dekuNukem/daytripper/resources/2.4 GHz Inverted F Antenna Eagle Library   fabiobaltieri_files/ifa-eagle.png

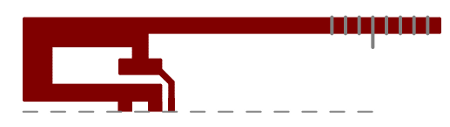
resources/2.4 GHz Inverted F Antenna Eagle Library fabiobaltieri_files/ifa-eagle.png
