dekuNukem/daytripper/resources/2.4 GHz Inverted F Antenna Eagle Library   fabiobaltieri_files/ifa.jpg

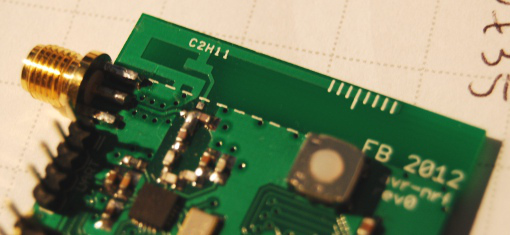
resources/2.4 GHz Inverted F Antenna Eagle Library fabiobaltieri_files/ifa.jpg
