dekuNukem/daytripper/resources/2.4 GHz Inverted F Antenna Eagle Library   fabiobaltieri_files/wpcom-gray-white.png

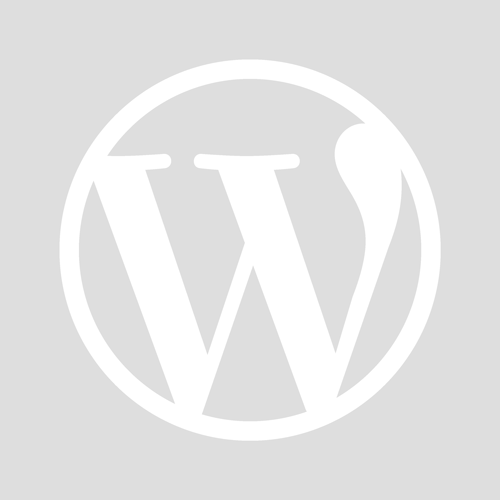
resources/2.4 GHz Inverted F Antenna Eagle Library fabiobaltieri_files/wpcom-gray-white.png
