dekuNukem/daytripper/firmware/distance_test/rx/MDK-ARM/rx/rx.htm

# Static Call Graph for image rx\rx.axf

#<CALLGRAPH># ARM Linker, 5060750: Last Updated: Sun Feb 24 13:35:41 2019

### Maximum Stack Usage = 220 bytes + Unknown(Cycles, Untraceable Function Pointers)

### Call chain for Maximum Stack Depth:

USB_IRQHandler ⇒ HAL_PCD_IRQHandler ⇒ HAL_PCD_ResumeCallback ⇒ SystemClock_Config ⇒ HAL_RCC_ClockConfig ⇒ HAL_RCC_GetSysClockFreq ⇒ __aeabi_uidivmod

### Mutually Recursive functions

- ADC1_IRQHandler ⇒ ADC1_IRQHandler
- HardFault_Handler ⇒ HardFault_Handler
- _Error_Handler ⇒ _Error_Handler

### Function Pointers

- ADC1_IRQHandler from startup_stm32f042x6.o(.text) referenced from startup_stm32f042x6.o(RESET)
- CEC_CAN_IRQHandler from startup_stm32f042x6.o(.text) referenced from startup_stm32f042x6.o(RESET)
- DMA1_Channel1_IRQHandler from startup_stm32f042x6.o(.text) referenced from startup_stm32f042x6.o(RESET)
- DMA1_Channel2_3_IRQHandler from startup_stm32f042x6.o(.text) referenced from startup_stm32f042x6.o(RESET)
- DMA1_Channel4_5_IRQHandler from startup_stm32f042x6.o(.text) referenced from startup_stm32f042x6.o(RESET)
- EXTI0_1_IRQHandler from startup_stm32f042x6.o(.text) referenced from startup_stm32f042x6.o(RESET)
- EXTI2_3_IRQHandler from startup_stm32f042x6.o(.text) referenced from startup_stm32f042x6.o(RESET)
- EXTI4_15_IRQHandler from startup_stm32f042x6.o(.text) referenced from startup_stm32f042x6.o(RESET)
- FLASH_IRQHandler from startup_stm32f042x6.o(.text) referenced from startup_stm32f042x6.o(RESET)
- HardFault_Handler from stm32f0xx_it.o(i.HardFault_Handler) referenced from startup_stm32f042x6.o(RESET)
- I2C1_IRQHandler from startup_stm32f042x6.o(.text) referenced from startup_stm32f042x6.o(RESET)
- NMI_Handler from stm32f0xx_it.o(i.NMI_Handler) referenced from startup_stm32f042x6.o(RESET)
- PVD_VDDIO2_IRQHandler from startup_stm32f042x6.o(.text) referenced from startup_stm32f042x6.o(RESET)
- PendSV_Handler from stm32f0xx_it.o(i.PendSV_Handler) referenced from startup_stm32f042x6.o(RESET)
- RCC_CRS_IRQHandler from startup_stm32f042x6.o(.text) referenced from startup_stm32f042x6.o(RESET)
- RTC_IRQHandler from startup_stm32f042x6.o(.text) referenced from startup_stm32f042x6.o(RESET)
- Reset_Handler from startup_stm32f042x6.o(.text) referenced from startup_stm32f042x6.o(RESET)
- SPI1_IRQHandler from startup_stm32f042x6.o(.text) referenced from startup_stm32f042x6.o(RESET)
- SPI2_IRQHandler from startup_stm32f042x6.o(.text) referenced from startup_stm32f042x6.o(RESET)
- SVC_Handler from stm32f0xx_it.o(i.SVC_Handler) referenced from startup_stm32f042x6.o(RESET)
- SysTick_Handler from stm32f0xx_it.o(i.SysTick_Handler) referenced from startup_stm32f042x6.o(RESET)
- SystemInit from system_stm32f0xx.o(i.SystemInit) referenced from startup_stm32f042x6.o(.text)
- TIM14_IRQHandler from startup_stm32f042x6.o(.text) referenced from startup_stm32f042x6.o(RESET)
- TIM16_IRQHandler from startup_stm32f042x6.o(.text) referenced from startup_stm32f042x6.o(RESET)
- TIM17_IRQHandler from startup_stm32f042x6.o(.text) referenced from startup_stm32f042x6.o(RESET)
- TIM1_BRK_UP_TRG_COM_IRQHandler from startup_stm32f042x6.o(.text) referenced from startup_stm32f042x6.o(RESET)
- TIM1_CC_IRQHandler from startup_stm32f042x6.o(.text) referenced from startup_stm32f042x6.o(RESET)
- TIM2_IRQHandler from startup_stm32f042x6.o(.text) referenced from startup_stm32f042x6.o(RESET)
- TIM3_IRQHandler from startup_stm32f042x6.o(.text) referenced from startup_stm32f042x6.o(RESET)
- TSC_IRQHandler from startup_stm32f042x6.o(.text) referenced from startup_stm32f042x6.o(RESET)
- USART1_IRQHandler from startup_stm32f042x6.o(.text) referenced from startup_stm32f042x6.o(RESET)
- USART2_IRQHandler from startup_stm32f042x6.o(.text) referenced from startup_stm32f042x6.o(RESET)
- USBD_FS_ConfigStrDescriptor from usbd_desc.o(i.USBD_FS_ConfigStrDescriptor) referenced from usbd_desc.o(.data)
- USBD_FS_DeviceDescriptor from usbd_desc.o(i.USBD_FS_DeviceDescriptor) referenced from usbd_desc.o(.data)
- USBD_FS_InterfaceStrDescriptor from usbd_desc.o(i.USBD_FS_InterfaceStrDescriptor) referenced from usbd_desc.o(.data)
- USBD_FS_LangIDStrDescriptor from usbd_desc.o(i.USBD_FS_LangIDStrDescriptor) referenced from usbd_desc.o(.data)
- USBD_FS_ManufacturerStrDescriptor from usbd_desc.o(i.USBD_FS_ManufacturerStrDescriptor) referenced from usbd_desc.o(.data)
- USBD_FS_ProductStrDescriptor from usbd_desc.o(i.USBD_FS_ProductStrDescriptor) referenced from usbd_desc.o(.data)
- USBD_FS_SerialStrDescriptor from usbd_desc.o(i.USBD_FS_SerialStrDescriptor) referenced from usbd_desc.o(.data)
- USBD_HID_DataIn from usbd_hid.o(i.USBD_HID_DataIn) referenced from usbd_hid.o(.data)
- USBD_HID_DeInit from usbd_hid.o(i.USBD_HID_DeInit) referenced from usbd_hid.o(.data)
- USBD_HID_GetCfgDesc from usbd_hid.o(i.USBD_HID_GetCfgDesc) referenced 3 times from usbd_hid.o(.data)
- USBD_HID_GetDeviceQualifierDesc from usbd_hid.o(i.USBD_HID_GetDeviceQualifierDesc) referenced from usbd_hid.o(.data)
- USBD_HID_Init from usbd_hid.o(i.USBD_HID_Init) referenced from usbd_hid.o(.data)
- USBD_HID_Setup from usbd_hid.o(i.USBD_HID_Setup) referenced from usbd_hid.o(.data)
- USB_IRQHandler from stm32f0xx_it.o(i.USB_IRQHandler) referenced from startup_stm32f042x6.o(RESET)
- WWDG_IRQHandler from startup_stm32f042x6.o(.text) referenced from startup_stm32f042x6.o(RESET)
- __main from entry.o(.ARM.Collect$$$$00000000) referenced from startup_stm32f042x6.o(.text)
- fputc from main.o(i.fputc) referenced from printf5.o(i.__0printf$5)
- main from main.o(i.main) referenced from entry9a.o(.ARM.Collect$$$$0000000B)

### Global Symbols

__main (Thumb, 0 bytes, Stack size unknown bytes, entry.o(.ARM.Collect$$$$00000000))
[Address Reference Count : 1]

- startup_stm32f042x6.o(.text)

_main_stk (Thumb, 0 bytes, Stack size unknown bytes, entry2.o(.ARM.Collect$$$$00000001))

_main_scatterload (Thumb, 0 bytes, Stack size unknown bytes, entry5.o(.ARM.Collect$$$$00000004))

[Calls]

- >> __scatterload

__main_after_scatterload (Thumb, 0 bytes, Stack size unknown bytes, entry5.o(.ARM.Collect$$$$00000004))

[Called By]

- >> __scatterload

_main_clock (Thumb, 0 bytes, Stack size unknown bytes, entry7b.o(.ARM.Collect$$$$00000008))

_main_cpp_init (Thumb, 0 bytes, Stack size unknown bytes, entry8b.o(.ARM.Collect$$$$0000000A))

_main_init (Thumb, 0 bytes, Stack size unknown bytes, entry9a.o(.ARM.Collect$$$$0000000B))

__rt_final_cpp (Thumb, 0 bytes, Stack size unknown bytes, entry10a.o(.ARM.Collect$$$$0000000D))

__rt_final_exit (Thumb, 0 bytes, Stack size unknown bytes, entry11a.o(.ARM.Collect$$$$0000000F))

Reset_Handler (Thumb, 38 bytes, Stack size 0 bytes, startup_stm32f042x6.o(.text))
[Address Reference Count : 1]

- startup_stm32f042x6.o(RESET)

ADC1_IRQHandler (Thumb, 0 bytes, Stack size 0 bytes, startup_stm32f042x6.o(.text))

[Calls]

- >> ADC1_IRQHandler

[Called By]

- >> ADC1_IRQHandler

[Address Reference Count : 1]

- startup_stm32f042x6.o(RESET)

CEC_CAN_IRQHandler (Thumb, 0 bytes, Stack size 0 bytes, startup_stm32f042x6.o(.text))
[Address Reference Count : 1]

- startup_stm32f042x6.o(RESET)

DMA1_Channel1_IRQHandler (Thumb, 0 bytes, Stack size 0 bytes, startup_stm32f042x6.o(.text))
[Address Reference Count : 1]

- startup_stm32f042x6.o(RESET)

DMA1_Channel2_3_IRQHandler (Thumb, 0 bytes, Stack size 0 bytes, startup_stm32f042x6.o(.text))
[Address Reference Count : 1]

- startup_stm32f042x6.o(RESET)

DMA1_Channel4_5_IRQHandler (Thumb, 0 bytes, Stack size 0 bytes, startup_stm32f042x6.o(.text))
[Address Reference Count : 1]

- startup_stm32f042x6.o(RESET)

EXTI0_1_IRQHandler (Thumb, 0 bytes, Stack size 0 bytes, startup_stm32f042x6.o(.text))
[Address Reference Count : 1]

- startup_stm32f042x6.o(RESET)

EXTI2_3_IRQHandler (Thumb, 0 bytes, Stack size 0 bytes, startup_stm32f042x6.o(.text))
[Address Reference Count : 1]

- startup_stm32f042x6.o(RESET)

EXTI4_15_IRQHandler (Thumb, 0 bytes, Stack size 0 bytes, startup_stm32f042x6.o(.text))
[Address Reference Count : 1]

- startup_stm32f042x6.o(RESET)

FLASH_IRQHandler (Thumb, 0 bytes, Stack size 0 bytes, startup_stm32f042x6.o(.text))
[Address Reference Count : 1]

- startup_stm32f042x6.o(RESET)

I2C1_IRQHandler (Thumb, 0 bytes, Stack size 0 bytes, startup_stm32f042x6.o(.text))
[Address Reference Count : 1]

- startup_stm32f042x6.o(RESET)

PVD_VDDIO2_IRQHandler (Thumb, 0 bytes, Stack size 0 bytes, startup_stm32f042x6.o(.text))
[Address Reference Count : 1]

- startup_stm32f042x6.o(RESET)

RCC_CRS_IRQHandler (Thumb, 0 bytes, Stack size 0 bytes, startup_stm32f042x6.o(.text))
[Address Reference Count : 1]

- startup_stm32f042x6.o(RESET)

RTC_IRQHandler (Thumb, 0 bytes, Stack size 0 bytes, startup_stm32f042x6.o(.text))
[Address Reference Count : 1]

- startup_stm32f042x6.o(RESET)

SPI1_IRQHandler (Thumb, 0 bytes, Stack size 0 bytes, startup_stm32f042x6.o(.text))
[Address Reference Count : 1]

- startup_stm32f042x6.o(RESET)

SPI2_IRQHandler (Thumb, 0 bytes, Stack size 0 bytes, startup_stm32f042x6.o(.text))
[Address Reference Count : 1]

- startup_stm32f042x6.o(RESET)

TIM14_IRQHandler (Thumb, 0 bytes, Stack size 0 bytes, startup_stm32f042x6.o(.text))
[Address Reference Count : 1]

- startup_stm32f042x6.o(RESET)

TIM16_IRQHandler (Thumb, 0 bytes, Stack size 0 bytes, startup_stm32f042x6.o(.text))
[Address Reference Count : 1]

- startup_stm32f042x6.o(RESET)

TIM17_IRQHandler (Thumb, 0 bytes, Stack size 0 bytes, startup_stm32f042x6.o(.text))
[Address Reference Count : 1]

- startup_stm32f042x6.o(RESET)

TIM1_BRK_UP_TRG_COM_IRQHandler (Thumb, 0 bytes, Stack size 0 bytes, startup_stm32f042x6.o(.text))
[Address Reference Count : 1]

- startup_stm32f042x6.o(RESET)

TIM1_CC_IRQHandler (Thumb, 0 bytes, Stack size 0 bytes, startup_stm32f042x6.o(.text))
[Address Reference Count : 1]

- startup_stm32f042x6.o(RESET)

TIM2_IRQHandler (Thumb, 0 bytes, Stack size 0 bytes, startup_stm32f042x6.o(.text))
[Address Reference Count : 1]

- startup_stm32f042x6.o(RESET)

TIM3_IRQHandler (Thumb, 0 bytes, Stack size 0 bytes, startup_stm32f042x6.o(.text))
[Address Reference Count : 1]

- startup_stm32f042x6.o(RESET)

TSC_IRQHandler (Thumb, 0 bytes, Stack size 0 bytes, startup_stm32f042x6.o(.text))
[Address Reference Count : 1]

- startup_stm32f042x6.o(RESET)

USART1_IRQHandler (Thumb, 0 bytes, Stack size 0 bytes, startup_stm32f042x6.o(.text))
[Address Reference Count : 1]

- startup_stm32f042x6.o(RESET)

USART2_IRQHandler (Thumb, 0 bytes, Stack size 0 bytes, startup_stm32f042x6.o(.text))
[Address Reference Count : 1]

- startup_stm32f042x6.o(RESET)

WWDG_IRQHandler (Thumb, 0 bytes, Stack size 0 bytes, startup_stm32f042x6.o(.text))
[Address Reference Count : 1]

- startup_stm32f042x6.o(RESET)

__aeabi_uidiv (Thumb, 0 bytes, Stack size 12 bytes, uidiv.o(.text), UNUSED)

__aeabi_uidivmod (Thumb, 44 bytes, Stack size 12 bytes, uidiv.o(.text))

[Stack]

- Max Depth = 12
- Call Chain = __aeabi_uidivmod

[Called By]

- >> USBD_LL_DataInStage
- >> SystemClock_Config
- >> HAL_InitTick
- >> HAL_RCC_GetSysClockFreq
- >> UART_SetConfig

__aeabi_llsr (Thumb, 34 bytes, Stack size 8 bytes, llushr.o(.text), UNUSED)

[Called By]

- >> __aeabi_uldivmod

_ll_ushift_r (Thumb, 0 bytes, Stack size 8 bytes, llushr.o(.text), UNUSED)

__aeabi_uldivmod (Thumb, 96 bytes, Stack size 48 bytes, uldiv.o(.text), UNUSED)

[Calls]

- >> __aeabi_llsr
- >> __aeabi_llsl

[Called By]

- >> _printf_core

__scatterload (Thumb, 28 bytes, Stack size 0 bytes, init.o(.text))

[Calls]

- >> __main_after_scatterload

[Called By]

- >> _main_scatterload

__scatterload_rt2 (Thumb, 0 bytes, Stack size 0 bytes, init.o(.text), UNUSED)

__aeabi_llsl (Thumb, 32 bytes, Stack size 8 bytes, llshl.o(.text), UNUSED)

[Called By]

- >> __aeabi_uldivmod

_ll_shift_l (Thumb, 0 bytes, Stack size 8 bytes, llshl.o(.text), UNUSED)

HAL_GPIO_Init (Thumb, 294 bytes, Stack size 24 bytes, stm32f0xx_hal_gpio.o(i.HAL_GPIO_Init))

[Stack]

- Max Depth = 24
- Call Chain = HAL_GPIO_Init

[Called By]

- >> MX_GPIO_Init
- >> HAL_UART_MspInit
- >> HAL_SPI_MspInit

HAL_GPIO_WritePin (Thumb, 12 bytes, Stack size 0 bytes, stm32f0xx_hal_gpio.o(i.HAL_GPIO_WritePin))

[Called By]

- >> main
- >> MX_GPIO_Init
- >> nrf24_csn_digitalWrite
- >> nrf24_ce_digitalWrite

HAL_GetTick (Thumb, 6 bytes, Stack size 0 bytes, stm32f0xx_hal.o(i.HAL_GetTick))

[Called By]

- >> HAL_UART_Transmit
- >> HAL_RCC_OscConfig
- >> HAL_RCC_ClockConfig
- >> HAL_RCCEx_PeriphCLKConfig
- >> HAL_SPI_TransmitReceive
- >> SPI_WaitFlagStateUntilTimeout
- >> SPI_WaitFifoStateUntilTimeout
- >> UART_WaitOnFlagUntilTimeout
- >> UART_CheckIdleState

HAL_HalfDuplex_Init (Thumb, 118 bytes, Stack size 16 bytes, stm32f0xx_hal_uart.o(i.HAL_HalfDuplex_Init))

[Stack]

- Max Depth = 100
- Call Chain = HAL_HalfDuplex_Init ⇒ UART_SetConfig ⇒ HAL_RCC_GetSysClockFreq ⇒ __aeabi_uidivmod

[Calls]

- >> HAL_UART_MspInit
- >> UART_SetConfig
- >> UART_CheckIdleState
- >> UART_AdvFeatureConfig

[Called By]

- >> MX_USART2_UART_Init

HAL_IncTick (Thumb, 10 bytes, Stack size 0 bytes, stm32f0xx_hal.o(i.HAL_IncTick))

[Called By]

- >> SysTick_Handler

HAL_Init (Thumb, 26 bytes, Stack size 8 bytes, stm32f0xx_hal.o(i.HAL_Init))

[Stack]

- Max Depth = 28
- Call Chain = HAL_Init ⇒ HAL_InitTick ⇒ __aeabi_uidivmod

[Calls]

- >> HAL_MspInit
- >> HAL_InitTick

[Called By]

- >> main

HAL_InitTick (Thumb, 34 bytes, Stack size 8 bytes, stm32f0xx_hal.o(i.HAL_InitTick))

[Stack]

- Max Depth = 20
- Call Chain = HAL_InitTick ⇒ __aeabi_uidivmod

[Calls]

- >> HAL_SYSTICK_Config
- >> HAL_RCC_GetHCLKFreq
- >> HAL_NVIC_SetPriority
- >> __aeabi_uidivmod

[Called By]

- >> HAL_RCC_ClockConfig
- >> HAL_Init

HAL_MspInit (Thumb, 74 bytes, Stack size 8 bytes, stm32f0xx_hal_msp.o(i.HAL_MspInit))

[Stack]

- Max Depth = 16
- Call Chain = HAL_MspInit ⇒ HAL_NVIC_SetPriority

[Calls]

- >> HAL_NVIC_SetPriority

[Called By]

- >> HAL_Init

HAL_NVIC_EnableIRQ (Thumb, 14 bytes, Stack size 0 bytes, stm32f0xx_hal_cortex.o(i.HAL_NVIC_EnableIRQ))

[Called By]

- >> HAL_PCD_MspInit

HAL_NVIC_SetPriority (Thumb, 8 bytes, Stack size 8 bytes, stm32f0xx_hal_cortex.o(i.HAL_NVIC_SetPriority))

[Stack]

- Max Depth = 8
- Call Chain = HAL_NVIC_SetPriority

[Calls]

- >> NVIC_SetPriority

[Called By]

- >> HAL_PCD_MspInit
- >> SystemClock_Config
- >> HAL_MspInit
- >> HAL_InitTick

HAL_PCDEx_PMAConfig (Thumb, 58 bytes, Stack size 8 bytes, stm32f0xx_hal_pcd_ex.o(i.HAL_PCDEx_PMAConfig))

[Stack]

- Max Depth = 8
- Call Chain = HAL_PCDEx_PMAConfig

[Called By]

- >> USBD_LL_Init

HAL_PCD_DataInStageCallback (Thumb, 24 bytes, Stack size 8 bytes, usbd_conf.o(i.HAL_PCD_DataInStageCallback))

[Stack]

- Max Depth = 84
- Call Chain = HAL_PCD_DataInStageCallback ⇒ USBD_LL_DataInStage ⇒ USBD_CtlContinueSendData ⇒ USBD_LL_Transmit ⇒ HAL_PCD_EP_Transmit ⇒ PCD_WritePMA

[Calls]

- >> USBD_LL_DataInStage

[Called By]

- >> PCD_EP_ISR_Handler

HAL_PCD_DataOutStageCallback (Thumb, 28 bytes, Stack size 8 bytes, usbd_conf.o(i.HAL_PCD_DataOutStageCallback))

[Stack]

- Max Depth = 68
- Call Chain = HAL_PCD_DataOutStageCallback ⇒ USBD_LL_DataOutStage ⇒ USBD_CtlSendStatus ⇒ USBD_LL_Transmit ⇒ HAL_PCD_EP_Transmit ⇒ PCD_WritePMA

[Calls]

- >> USBD_LL_DataOutStage

[Called By]

- >> PCD_EP_ISR_Handler

HAL_PCD_EP_Close (Thumb, 346 bytes, Stack size 20 bytes, stm32f0xx_hal_pcd.o(i.HAL_PCD_EP_Close))

[Stack]

- Max Depth = 20
- Call Chain = HAL_PCD_EP_Close

[Called By]

- >> USBD_LL_CloseEP

HAL_PCD_EP_ClrStall (Thumb, 166 bytes, Stack size 20 bytes, stm32f0xx_hal_pcd.o(i.HAL_PCD_EP_ClrStall))

[Stack]

- Max Depth = 20
- Call Chain = HAL_PCD_EP_ClrStall

[Called By]

- >> USBD_LL_ClearStallEP

HAL_PCD_EP_Open (Thumb, 652 bytes, Stack size 20 bytes, stm32f0xx_hal_pcd.o(i.HAL_PCD_EP_Open))

[Stack]

- Max Depth = 20
- Call Chain = HAL_PCD_EP_Open

[Called By]

- >> USBD_LL_OpenEP

HAL_PCD_EP_Receive (Thumb, 244 bytes, Stack size 20 bytes, stm32f0xx_hal_pcd.o(i.HAL_PCD_EP_Receive))

[Stack]

- Max Depth = 20
- Call Chain = HAL_PCD_EP_Receive

[Called By]

- >> USBD_LL_PrepareReceive
- >> PCD_EP_ISR_Handler

HAL_PCD_EP_SetStall (Thumb, 136 bytes, Stack size 20 bytes, stm32f0xx_hal_pcd.o(i.HAL_PCD_EP_SetStall))

[Stack]

- Max Depth = 20
- Call Chain = HAL_PCD_EP_SetStall

[Called By]

- >> USBD_LL_StallEP

HAL_PCD_EP_Transmit (Thumb, 222 bytes, Stack size 20 bytes, stm32f0xx_hal_pcd.o(i.HAL_PCD_EP_Transmit))

[Stack]

- Max Depth = 28
- Call Chain = HAL_PCD_EP_Transmit ⇒ PCD_WritePMA

[Calls]

- >> PCD_WritePMA

[Called By]

- >> USBD_LL_Transmit
- >> PCD_EP_ISR_Handler

HAL_PCD_IRQHandler (Thumb, 238 bytes, Stack size 16 bytes, stm32f0xx_hal_pcd.o(i.HAL_PCD_IRQHandler))

[Stack]

- Max Depth = 212
- Call Chain = HAL_PCD_IRQHandler ⇒ HAL_PCD_ResumeCallback ⇒ SystemClock_Config ⇒ HAL_RCC_ClockConfig ⇒ HAL_RCC_GetSysClockFreq ⇒ __aeabi_uidivmod

[Calls]

- >> HAL_PCD_SetAddress
- >> HAL_PCD_SuspendCallback
- >> HAL_PCD_SOFCallback
- >> HAL_PCD_ResumeCallback
- >> HAL_PCD_ResetCallback
- >> PCD_EP_ISR_Handler

[Called By]

- >> USB_IRQHandler

HAL_PCD_Init (Thumb, 154 bytes, Stack size 24 bytes, stm32f0xx_hal_pcd.o(i.HAL_PCD_Init))

[Stack]

- Max Depth = 40
- Call Chain = HAL_PCD_Init ⇒ HAL_PCD_MspInit ⇒ HAL_NVIC_SetPriority

[Calls]

- >> HAL_PCD_MspInit

[Called By]

- >> USBD_LL_Init

HAL_PCD_MspInit (Thumb, 46 bytes, Stack size 8 bytes, usbd_conf.o(i.HAL_PCD_MspInit))

[Stack]

- Max Depth = 16
- Call Chain = HAL_PCD_MspInit ⇒ HAL_NVIC_SetPriority

[Calls]

- >> HAL_NVIC_EnableIRQ
- >> HAL_NVIC_SetPriority

[Called By]

- >> HAL_PCD_Init

HAL_PCD_ResetCallback (Thumb, 24 bytes, Stack size 8 bytes, usbd_conf.o(i.HAL_PCD_ResetCallback))

[Stack]

- Max Depth = 60
- Call Chain = HAL_PCD_ResetCallback ⇒ USBD_LL_Reset ⇒ USBD_LL_OpenEP ⇒ HAL_PCD_EP_Open

[Calls]

- >> USBD_LL_SetSpeed
- >> USBD_LL_Reset

[Called By]

- >> HAL_PCD_IRQHandler

HAL_PCD_ResumeCallback (Thumb, 38 bytes, Stack size 8 bytes, usbd_conf.o(i.HAL_PCD_ResumeCallback))

[Stack]

- Max Depth = 196
- Call Chain = HAL_PCD_ResumeCallback ⇒ SystemClock_Config ⇒ HAL_RCC_ClockConfig ⇒ HAL_RCC_GetSysClockFreq ⇒ __aeabi_uidivmod

[Calls]

- >> USBD_LL_Resume
- >> SystemClock_Config

[Called By]

- >> HAL_PCD_IRQHandler

HAL_PCD_SOFCallback (Thumb, 16 bytes, Stack size 8 bytes, usbd_conf.o(i.HAL_PCD_SOFCallback))

[Stack]

- Max Depth = 16
- Call Chain = HAL_PCD_SOFCallback ⇒ USBD_LL_SOF

[Calls]

- >> USBD_LL_SOF

[Called By]

- >> HAL_PCD_IRQHandler

HAL_PCD_SetAddress (Thumb, 44 bytes, Stack size 0 bytes, stm32f0xx_hal_pcd.o(i.HAL_PCD_SetAddress))

[Called By]

- >> USBD_LL_SetUSBAddress
- >> HAL_PCD_IRQHandler

HAL_PCD_SetupStageCallback (Thumb, 22 bytes, Stack size 8 bytes, usbd_conf.o(i.HAL_PCD_SetupStageCallback))

[Stack]

- Max Depth = 116
- Call Chain = HAL_PCD_SetupStageCallback ⇒ USBD_LL_SetupStage ⇒ USBD_StdDevReq ⇒ USBD_GetDescriptor ⇒ USBD_CtlSendData ⇒ USBD_LL_Transmit ⇒ HAL_PCD_EP_Transmit ⇒ PCD_WritePMA

[Calls]

- >> USBD_LL_SetupStage

[Called By]

- >> PCD_EP_ISR_Handler

HAL_PCD_Start (Thumb, 18 bytes, Stack size 0 bytes, stm32f0xx_hal_pcd.o(i.HAL_PCD_Start))

[Called By]

- >> USBD_LL_Start

HAL_PCD_SuspendCallback (Thumb, 34 bytes, Stack size 8 bytes, usbd_conf.o(i.HAL_PCD_SuspendCallback))

[Stack]

- Max Depth = 8
- Call Chain = HAL_PCD_SuspendCallback

[Calls]

- >> USBD_LL_Suspend

[Called By]

- >> HAL_PCD_IRQHandler

HAL_RCCEx_PeriphCLKConfig (Thumb, 254 bytes, Stack size 24 bytes, stm32f0xx_hal_rcc_ex.o(i.HAL_RCCEx_PeriphCLKConfig))

[Stack]

- Max Depth = 24
- Call Chain = HAL_RCCEx_PeriphCLKConfig

[Calls]

- >> HAL_GetTick

[Called By]

- >> SystemClock_Config

HAL_RCC_ClockConfig (Thumb, 320 bytes, Stack size 24 bytes, stm32f0xx_hal_rcc.o(i.HAL_RCC_ClockConfig))

[Stack]

- Max Depth = 84
- Call Chain = HAL_RCC_ClockConfig ⇒ HAL_RCC_GetSysClockFreq ⇒ __aeabi_uidivmod

[Calls]

- >> HAL_GetTick
- >> HAL_InitTick
- >> HAL_RCC_GetSysClockFreq

[Called By]

- >> SystemClock_Config

HAL_RCC_GetHCLKFreq (Thumb, 6 bytes, Stack size 0 bytes, stm32f0xx_hal_rcc.o(i.HAL_RCC_GetHCLKFreq))

[Called By]

- >> SystemClock_Config
- >> HAL_InitTick

HAL_RCC_GetPCLK1Freq (Thumb, 20 bytes, Stack size 0 bytes, stm32f0xx_hal_rcc.o(i.HAL_RCC_GetPCLK1Freq))

[Called By]

- >> UART_SetConfig

HAL_RCC_GetSysClockFreq (Thumb, 90 bytes, Stack size 48 bytes, stm32f0xx_hal_rcc.o(i.HAL_RCC_GetSysClockFreq))

[Stack]

- Max Depth = 60
- Call Chain = HAL_RCC_GetSysClockFreq ⇒ __aeabi_uidivmod

[Calls]

- >> __aeabi_uidivmod

[Called By]

- >> HAL_RCC_ClockConfig
- >> UART_SetConfig

HAL_RCC_OscConfig (Thumb, 966 bytes, Stack size 32 bytes, stm32f0xx_hal_rcc.o(i.HAL_RCC_OscConfig))

[Stack]

- Max Depth = 32
- Call Chain = HAL_RCC_OscConfig

[Calls]

- >> HAL_GetTick

[Called By]

- >> SystemClock_Config

HAL_SPI_Init (Thumb, 184 bytes, Stack size 24 bytes, stm32f0xx_hal_spi.o(i.HAL_SPI_Init))

[Stack]

- Max Depth = 80
- Call Chain = HAL_SPI_Init ⇒ HAL_SPI_MspInit ⇒ HAL_GPIO_Init

[Calls]

- >> HAL_SPI_MspInit

[Called By]

- >> MX_SPI1_Init

HAL_SPI_MspInit (Thumb, 60 bytes, Stack size 32 bytes, stm32f0xx_hal_msp.o(i.HAL_SPI_MspInit))

[Stack]

- Max Depth = 56
- Call Chain = HAL_SPI_MspInit ⇒ HAL_GPIO_Init

[Calls]

- >> HAL_GPIO_Init

[Called By]

- >> HAL_SPI_Init

HAL_SPI_TransmitReceive (Thumb, 584 bytes, Stack size 48 bytes, stm32f0xx_hal_spi.o(i.HAL_SPI_TransmitReceive))

[Stack]

- Max Depth = 96
- Call Chain = HAL_SPI_TransmitReceive ⇒ SPI_EndRxTxTransaction ⇒ SPI_WaitFlagStateUntilTimeout

[Calls]

- >> HAL_GetTick
- >> SPI_EndRxTxTransaction

[Called By]

- >> spi_transfer

HAL_SYSTICK_CLKSourceConfig (Thumb, 20 bytes, Stack size 0 bytes, stm32f0xx_hal_cortex.o(i.HAL_SYSTICK_CLKSourceConfig))

[Called By]

- >> SystemClock_Config

HAL_SYSTICK_Callback (Thumb, 2 bytes, Stack size 0 bytes, stm32f0xx_hal_cortex.o(i.HAL_SYSTICK_Callback))

[Called By]

- >> HAL_SYSTICK_IRQHandler

HAL_SYSTICK_Config (Thumb, 38 bytes, Stack size 8 bytes, stm32f0xx_hal_cortex.o(i.HAL_SYSTICK_Config))

[Stack]

- Max Depth = 8
- Call Chain = HAL_SYSTICK_Config

[Calls]

- >> NVIC_SetPriority

[Called By]

- >> SystemClock_Config
- >> HAL_InitTick

HAL_SYSTICK_IRQHandler (Thumb, 8 bytes, Stack size 8 bytes, stm32f0xx_hal_cortex.o(i.HAL_SYSTICK_IRQHandler))

[Stack]

- Max Depth = 8
- Call Chain = HAL_SYSTICK_IRQHandler

[Calls]

- >> HAL_SYSTICK_Callback

[Called By]

- >> SysTick_Handler

HAL_UART_MspInit (Thumb, 62 bytes, Stack size 32 bytes, stm32f0xx_hal_msp.o(i.HAL_UART_MspInit))

[Stack]

- Max Depth = 56
- Call Chain = HAL_UART_MspInit ⇒ HAL_GPIO_Init

[Calls]

- >> HAL_GPIO_Init

[Called By]

- >> HAL_HalfDuplex_Init

HAL_UART_Transmit (Thumb, 200 bytes, Stack size 48 bytes, stm32f0xx_hal_uart.o(i.HAL_UART_Transmit))

[Stack]

- Max Depth = 88
- Call Chain = HAL_UART_Transmit ⇒ UART_WaitOnFlagUntilTimeout

[Calls]

- >> HAL_GetTick
- >> UART_WaitOnFlagUntilTimeout

[Called By]

- >> fputc

HardFault_Handler (Thumb, 2 bytes, Stack size 0 bytes, stm32f0xx_it.o(i.HardFault_Handler))

[Calls]

- >> HardFault_Handler

[Called By]

- >> HardFault_Handler

[Address Reference Count : 1]

- startup_stm32f042x6.o(RESET)

MX_USB_DEVICE_Init (Thumb, 28 bytes, Stack size 8 bytes, usb_device.o(i.MX_USB_DEVICE_Init))

[Stack]

- Max Depth = 64
- Call Chain = MX_USB_DEVICE_Init ⇒ USBD_Init ⇒ USBD_LL_Init ⇒ HAL_PCD_Init ⇒ HAL_PCD_MspInit ⇒ HAL_NVIC_SetPriority

[Calls]

- >> USBD_Start
- >> USBD_RegisterClass
- >> USBD_Init

[Called By]

- >> main

NMI_Handler (Thumb, 2 bytes, Stack size 0 bytes, stm32f0xx_it.o(i.NMI_Handler))
[Address Reference Count : 1]

- startup_stm32f042x6.o(RESET)

PCD_ReadPMA (Thumb, 42 bytes, Stack size 8 bytes, stm32f0xx_hal_pcd.o(i.PCD_ReadPMA))

[Stack]

- Max Depth = 8
- Call Chain = PCD_ReadPMA

[Called By]

- >> PCD_EP_ISR_Handler

PCD_WritePMA (Thumb, 38 bytes, Stack size 8 bytes, stm32f0xx_hal_pcd.o(i.PCD_WritePMA))

[Stack]

- Max Depth = 8
- Call Chain = PCD_WritePMA

[Called By]

- >> HAL_PCD_EP_Transmit
- >> PCD_EP_ISR_Handler

PendSV_Handler (Thumb, 2 bytes, Stack size 0 bytes, stm32f0xx_it.o(i.PendSV_Handler))
[Address Reference Count : 1]

- startup_stm32f042x6.o(RESET)

SVC_Handler (Thumb, 2 bytes, Stack size 0 bytes, stm32f0xx_it.o(i.SVC_Handler))
[Address Reference Count : 1]

- startup_stm32f042x6.o(RESET)

SysTick_Handler (Thumb, 12 bytes, Stack size 8 bytes, stm32f0xx_it.o(i.SysTick_Handler))

[Stack]

- Max Depth = 16
- Call Chain = SysTick_Handler ⇒ HAL_SYSTICK_IRQHandler

[Calls]

- >> HAL_SYSTICK_IRQHandler
- >> HAL_IncTick

[Address Reference Count : 1]

- startup_stm32f042x6.o(RESET)

SystemClock_Config (Thumb, 110 bytes, Stack size 104 bytes, main.o(i.SystemClock_Config))

[Stack]

- Max Depth = 188
- Call Chain = SystemClock_Config ⇒ HAL_RCC_ClockConfig ⇒ HAL_RCC_GetSysClockFreq ⇒ __aeabi_uidivmod

[Calls]

- >> HAL_SYSTICK_Config
- >> HAL_SYSTICK_CLKSourceConfig
- >> HAL_RCC_OscConfig
- >> HAL_RCC_GetHCLKFreq
- >> HAL_RCC_ClockConfig
- >> HAL_RCCEx_PeriphCLKConfig
- >> HAL_NVIC_SetPriority
- >> __aeabi_uidivmod

[Called By]

- >> HAL_PCD_ResumeCallback
- >> main

SystemInit (Thumb, 78 bytes, Stack size 0 bytes, system_stm32f0xx.o(i.SystemInit))
[Address Reference Count : 1]

- startup_stm32f042x6.o(.text)

UART_AdvFeatureConfig (Thumb, 202 bytes, Stack size 8 bytes, stm32f0xx_hal_uart.o(i.UART_AdvFeatureConfig))

[Stack]

- Max Depth = 8
- Call Chain = UART_AdvFeatureConfig

[Called By]

- >> HAL_HalfDuplex_Init

UART_CheckIdleState (Thumb, 96 bytes, Stack size 24 bytes, stm32f0xx_hal_uart.o(i.UART_CheckIdleState))

[Stack]

- Max Depth = 64
- Call Chain = UART_CheckIdleState ⇒ UART_WaitOnFlagUntilTimeout

[Calls]

- >> HAL_GetTick
- >> UART_WaitOnFlagUntilTimeout

[Called By]

- >> HAL_HalfDuplex_Init

UART_SetConfig (Thumb, 280 bytes, Stack size 24 bytes, stm32f0xx_hal_uart.o(i.UART_SetConfig))

[Stack]

- Max Depth = 84
- Call Chain = UART_SetConfig ⇒ HAL_RCC_GetSysClockFreq ⇒ __aeabi_uidivmod

[Calls]

- >> HAL_RCC_GetSysClockFreq
- >> HAL_RCC_GetPCLK1Freq
- >> __aeabi_uidivmod

[Called By]

- >> HAL_HalfDuplex_Init

UART_WaitOnFlagUntilTimeout (Thumb, 98 bytes, Stack size 40 bytes, stm32f0xx_hal_uart.o(i.UART_WaitOnFlagUntilTimeout))

[Stack]

- Max Depth = 40
- Call Chain = UART_WaitOnFlagUntilTimeout

[Calls]

- >> HAL_GetTick

[Called By]

- >> HAL_UART_Transmit
- >> UART_CheckIdleState

USBD_ClrClassConfig (Thumb, 16 bytes, Stack size 8 bytes, usbd_core.o(i.USBD_ClrClassConfig))

[Stack]

- Max Depth = 8
- Call Chain = USBD_ClrClassConfig

[Called By]

- >> USBD_SetConfig

USBD_CtlContinueRx (Thumb, 16 bytes, Stack size 8 bytes, usbd_ioreq.o(i.USBD_CtlContinueRx))

[Stack]

- Max Depth = 36
- Call Chain = USBD_CtlContinueRx ⇒ USBD_LL_PrepareReceive ⇒ HAL_PCD_EP_Receive

[Calls]

- >> USBD_LL_PrepareReceive

[Called By]

- >> USBD_LL_DataOutStage

USBD_CtlContinueSendData (Thumb, 16 bytes, Stack size 8 bytes, usbd_ioreq.o(i.USBD_CtlContinueSendData))

[Stack]

- Max Depth = 44
- Call Chain = USBD_CtlContinueSendData ⇒ USBD_LL_Transmit ⇒ HAL_PCD_EP_Transmit ⇒ PCD_WritePMA

[Calls]

- >> USBD_LL_Transmit

[Called By]

- >> USBD_LL_DataInStage

USBD_CtlError (Thumb, 20 bytes, Stack size 8 bytes, usbd_ctlreq.o(i.USBD_CtlError))

[Stack]

- Max Depth = 36
- Call Chain = USBD_CtlError ⇒ USBD_LL_StallEP ⇒ HAL_PCD_EP_SetStall

[Calls]

- >> USBD_LL_StallEP

[Called By]

- >> USBD_HID_Setup
- >> USBD_SetConfig
- >> USBD_GetDescriptor
- >> USBD_StdItfReq
- >> USBD_StdEPReq
- >> USBD_StdDevReq

USBD_CtlReceiveStatus (Thumb, 24 bytes, Stack size 8 bytes, usbd_ioreq.o(i.USBD_CtlReceiveStatus))

[Stack]

- Max Depth = 36
- Call Chain = USBD_CtlReceiveStatus ⇒ USBD_LL_PrepareReceive ⇒ HAL_PCD_EP_Receive

[Calls]

- >> USBD_LL_PrepareReceive

[Called By]

- >> USBD_LL_DataInStage

USBD_CtlSendData (Thumb, 28 bytes, Stack size 8 bytes, usbd_ioreq.o(i.USBD_CtlSendData))

[Stack]

- Max Depth = 44
- Call Chain = USBD_CtlSendData ⇒ USBD_LL_Transmit ⇒ HAL_PCD_EP_Transmit ⇒ PCD_WritePMA

[Calls]

- >> USBD_LL_Transmit

[Called By]

- >> USBD_HID_Setup
- >> USBD_GetDescriptor
- >> USBD_StdEPReq
- >> USBD_StdDevReq

USBD_CtlSendStatus (Thumb, 24 bytes, Stack size 8 bytes, usbd_ioreq.o(i.USBD_CtlSendStatus))

[Stack]

- Max Depth = 44
- Call Chain = USBD_CtlSendStatus ⇒ USBD_LL_Transmit ⇒ HAL_PCD_EP_Transmit ⇒ PCD_WritePMA

[Calls]

- >> USBD_LL_Transmit

[Called By]

- >> USBD_LL_DataOutStage
- >> USBD_SetConfig
- >> USBD_StdItfReq
- >> USBD_StdEPReq
- >> USBD_StdDevReq

USBD_FS_ConfigStrDescriptor (Thumb, 16 bytes, Stack size 8 bytes, usbd_desc.o(i.USBD_FS_ConfigStrDescriptor))

[Stack]

- Max Depth = 24
- Call Chain = USBD_FS_ConfigStrDescriptor ⇒ USBD_GetString

[Calls]

- >> USBD_GetString

[Address Reference Count : 1]

- usbd_desc.o(.data)

USBD_FS_DeviceDescriptor (Thumb, 8 bytes, Stack size 0 bytes, usbd_desc.o(i.USBD_FS_DeviceDescriptor))
[Address Reference Count : 1]

- usbd_desc.o(.data)

USBD_FS_InterfaceStrDescriptor (Thumb, 16 bytes, Stack size 8 bytes, usbd_desc.o(i.USBD_FS_InterfaceStrDescriptor))

[Stack]

- Max Depth = 24
- Call Chain = USBD_FS_InterfaceStrDescriptor ⇒ USBD_GetString

[Calls]

- >> USBD_GetString

[Address Reference Count : 1]

- usbd_desc.o(.data)

USBD_FS_LangIDStrDescriptor (Thumb, 8 bytes, Stack size 0 bytes, usbd_desc.o(i.USBD_FS_LangIDStrDescriptor))
[Address Reference Count : 1]

- usbd_desc.o(.data)

USBD_FS_ManufacturerStrDescriptor (Thumb, 16 bytes, Stack size 8 bytes, usbd_desc.o(i.USBD_FS_ManufacturerStrDescriptor))

[Stack]

- Max Depth = 24
- Call Chain = USBD_FS_ManufacturerStrDescriptor ⇒ USBD_GetString

[Calls]

- >> USBD_GetString

[Address Reference Count : 1]

- usbd_desc.o(.data)

USBD_FS_ProductStrDescriptor (Thumb, 16 bytes, Stack size 8 bytes, usbd_desc.o(i.USBD_FS_ProductStrDescriptor))

[Stack]

- Max Depth = 24
- Call Chain = USBD_FS_ProductStrDescriptor ⇒ USBD_GetString

[Calls]

- >> USBD_GetString

[Address Reference Count : 1]

- usbd_desc.o(.data)

USBD_FS_SerialStrDescriptor (Thumb, 16 bytes, Stack size 8 bytes, usbd_desc.o(i.USBD_FS_SerialStrDescriptor))

[Stack]

- Max Depth = 24
- Call Chain = USBD_FS_SerialStrDescriptor ⇒ USBD_GetString

[Calls]

- >> USBD_GetString

[Address Reference Count : 1]

- usbd_desc.o(.data)

USBD_GetString (Thumb, 68 bytes, Stack size 16 bytes, usbd_ctlreq.o(i.USBD_GetString))

[Stack]

- Max Depth = 16
- Call Chain = USBD_GetString

[Called By]

- >> USBD_FS_SerialStrDescriptor
- >> USBD_FS_ProductStrDescriptor
- >> USBD_FS_ManufacturerStrDescriptor
- >> USBD_FS_InterfaceStrDescriptor
- >> USBD_FS_ConfigStrDescriptor

USBD_Init (Thumb, 50 bytes, Stack size 8 bytes, usbd_core.o(i.USBD_Init))

[Stack]

- Max Depth = 56
- Call Chain = USBD_Init ⇒ USBD_LL_Init ⇒ HAL_PCD_Init ⇒ HAL_PCD_MspInit ⇒ HAL_NVIC_SetPriority

[Calls]

- >> USBD_LL_Init

[Called By]

- >> MX_USB_DEVICE_Init

USBD_LL_ClearStallEP (Thumb, 38 bytes, Stack size 8 bytes, usbd_conf.o(i.USBD_LL_ClearStallEP))

[Stack]

- Max Depth = 28
- Call Chain = USBD_LL_ClearStallEP ⇒ HAL_PCD_EP_ClrStall

[Calls]

- >> HAL_PCD_EP_ClrStall

[Called By]

- >> USBD_StdEPReq

USBD_LL_CloseEP (Thumb, 38 bytes, Stack size 8 bytes, usbd_conf.o(i.USBD_LL_CloseEP))

[Stack]

- Max Depth = 28
- Call Chain = USBD_LL_CloseEP ⇒ HAL_PCD_EP_Close

[Calls]

- >> HAL_PCD_EP_Close

[Called By]

- >> USBD_HID_DeInit

USBD_LL_DataInStage (Thumb, 182 bytes, Stack size 32 bytes, usbd_core.o(i.USBD_LL_DataInStage))

[Stack]

- Max Depth = 76
- Call Chain = USBD_LL_DataInStage ⇒ USBD_CtlContinueSendData ⇒ USBD_LL_Transmit ⇒ HAL_PCD_EP_Transmit ⇒ PCD_WritePMA

[Calls]

- >> USBD_LL_PrepareReceive
- >> __aeabi_uidivmod
- >> USBD_CtlReceiveStatus
- >> USBD_CtlContinueSendData

[Called By]

- >> HAL_PCD_DataInStageCallback

USBD_LL_DataOutStage (Thumb, 116 bytes, Stack size 16 bytes, usbd_core.o(i.USBD_LL_DataOutStage))

[Stack]

- Max Depth = 60
- Call Chain = USBD_LL_DataOutStage ⇒ USBD_CtlSendStatus ⇒ USBD_LL_Transmit ⇒ HAL_PCD_EP_Transmit ⇒ PCD_WritePMA

[Calls]

- >> USBD_CtlSendStatus
- >> USBD_CtlContinueRx

[Called By]

- >> HAL_PCD_DataOutStageCallback

USBD_LL_Init (Thumb, 102 bytes, Stack size 8 bytes, usbd_conf.o(i.USBD_LL_Init))

[Stack]

- Max Depth = 48
- Call Chain = USBD_LL_Init ⇒ HAL_PCD_Init ⇒ HAL_PCD_MspInit ⇒ HAL_NVIC_SetPriority

[Calls]

- >> HAL_PCD_Init
- >> HAL_PCDEx_PMAConfig
- >> _Error_Handler

[Called By]

- >> USBD_Init

USBD_LL_IsStallEP (Thumb, 36 bytes, Stack size 0 bytes, usbd_conf.o(i.USBD_LL_IsStallEP))

[Called By]

- >> USBD_StdEPReq

USBD_LL_OpenEP (Thumb, 44 bytes, Stack size 16 bytes, usbd_conf.o(i.USBD_LL_OpenEP))

[Stack]

- Max Depth = 36
- Call Chain = USBD_LL_OpenEP ⇒ HAL_PCD_EP_Open

[Calls]

- >> HAL_PCD_EP_Open

[Called By]

- >> USBD_LL_Reset
- >> USBD_HID_Init

USBD_LL_PrepareReceive (Thumb, 38 bytes, Stack size 8 bytes, usbd_conf.o(i.USBD_LL_PrepareReceive))

[Stack]

- Max Depth = 28
- Call Chain = USBD_LL_PrepareReceive ⇒ HAL_PCD_EP_Receive

[Calls]

- >> HAL_PCD_EP_Receive

[Called By]

- >> USBD_LL_DataInStage
- >> USBD_CtlReceiveStatus
- >> USBD_CtlContinueRx

USBD_LL_Reset (Thumb, 70 bytes, Stack size 16 bytes, usbd_core.o(i.USBD_LL_Reset))

[Stack]

- Max Depth = 52
- Call Chain = USBD_LL_Reset ⇒ USBD_LL_OpenEP ⇒ HAL_PCD_EP_Open

[Calls]

- >> USBD_LL_OpenEP

[Called By]

- >> HAL_PCD_ResetCallback

USBD_LL_Resume (Thumb, 12 bytes, Stack size 0 bytes, usbd_core.o(i.USBD_LL_Resume))

[Called By]

- >> HAL_PCD_ResumeCallback

USBD_LL_SOF (Thumb, 30 bytes, Stack size 8 bytes, usbd_core.o(i.USBD_LL_SOF))

[Stack]

- Max Depth = 8
- Call Chain = USBD_LL_SOF

[Called By]

- >> HAL_PCD_SOFCallback

USBD_LL_SetSpeed (Thumb, 6 bytes, Stack size 0 bytes, usbd_core.o(i.USBD_LL_SetSpeed))

[Called By]

- >> HAL_PCD_ResetCallback

USBD_LL_SetUSBAddress (Thumb, 38 bytes, Stack size 8 bytes, usbd_conf.o(i.USBD_LL_SetUSBAddress))

[Stack]

- Max Depth = 8
- Call Chain = USBD_LL_SetUSBAddress

[Calls]

- >> HAL_PCD_SetAddress

[Called By]

- >> USBD_StdDevReq

USBD_LL_SetupStage (Thumb, 94 bytes, Stack size 16 bytes, usbd_core.o(i.USBD_LL_SetupStage))

[Stack]

- Max Depth = 108
- Call Chain = USBD_LL_SetupStage ⇒ USBD_StdDevReq ⇒ USBD_GetDescriptor ⇒ USBD_CtlSendData ⇒ USBD_LL_Transmit ⇒ HAL_PCD_EP_Transmit ⇒ PCD_WritePMA

[Calls]

- >> USBD_LL_StallEP
- >> USBD_StdItfReq
- >> USBD_StdEPReq
- >> USBD_StdDevReq
- >> USBD_ParseSetupRequest

[Called By]

- >> HAL_PCD_SetupStageCallback

USBD_LL_StallEP (Thumb, 38 bytes, Stack size 8 bytes, usbd_conf.o(i.USBD_LL_StallEP))

[Stack]

- Max Depth = 28
- Call Chain = USBD_LL_StallEP ⇒ HAL_PCD_EP_SetStall

[Calls]

- >> HAL_PCD_EP_SetStall

[Called By]

- >> USBD_LL_SetupStage
- >> USBD_CtlError
- >> USBD_StdEPReq

USBD_LL_Start (Thumb, 38 bytes, Stack size 8 bytes, usbd_conf.o(i.USBD_LL_Start))

[Stack]

- Max Depth = 8
- Call Chain = USBD_LL_Start

[Calls]

- >> HAL_PCD_Start

[Called By]

- >> USBD_Start

USBD_LL_Suspend (Thumb, 16 bytes, Stack size 0 bytes, usbd_core.o(i.USBD_LL_Suspend))

[Called By]

- >> HAL_PCD_SuspendCallback

USBD_LL_Transmit (Thumb, 38 bytes, Stack size 8 bytes, usbd_conf.o(i.USBD_LL_Transmit))

[Stack]

- Max Depth = 36
- Call Chain = USBD_LL_Transmit ⇒ HAL_PCD_EP_Transmit ⇒ PCD_WritePMA

[Calls]

- >> HAL_PCD_EP_Transmit

[Called By]

- >> USBD_CtlSendData
- >> USBD_CtlSendStatus
- >> USBD_CtlContinueSendData

USBD_ParseSetupRequest (Thumb, 40 bytes, Stack size 0 bytes, usbd_ctlreq.o(i.USBD_ParseSetupRequest))

[Called By]

- >> USBD_LL_SetupStage

USBD_RegisterClass (Thumb, 22 bytes, Stack size 0 bytes, usbd_core.o(i.USBD_RegisterClass))

[Called By]

- >> MX_USB_DEVICE_Init

USBD_SetClassConfig (Thumb, 28 bytes, Stack size 8 bytes, usbd_core.o(i.USBD_SetClassConfig))

[Stack]

- Max Depth = 8
- Call Chain = USBD_SetClassConfig

[Called By]

- >> USBD_SetConfig

USBD_Start (Thumb, 10 bytes, Stack size 8 bytes, usbd_core.o(i.USBD_Start))

[Stack]

- Max Depth = 16
- Call Chain = USBD_Start ⇒ USBD_LL_Start

[Calls]

- >> USBD_LL_Start

[Called By]

- >> MX_USB_DEVICE_Init

USBD_StdDevReq (Thumb, 238 bytes, Stack size 24 bytes, usbd_ctlreq.o(i.USBD_StdDevReq))

[Stack]

- Max Depth = 92
- Call Chain = USBD_StdDevReq ⇒ USBD_GetDescriptor ⇒ USBD_CtlSendData ⇒ USBD_LL_Transmit ⇒ HAL_PCD_EP_Transmit ⇒ PCD_WritePMA

[Calls]

- >> USBD_LL_SetUSBAddress
- >> USBD_CtlSendData
- >> USBD_CtlError
- >> USBD_SetConfig
- >> USBD_GetDescriptor
- >> USBD_CtlSendStatus
- >> __ARM_common_switch8

[Called By]

- >> USBD_LL_SetupStage

USBD_StdEPReq (Thumb, 234 bytes, Stack size 24 bytes, usbd_ctlreq.o(i.USBD_StdEPReq))

[Stack]

- Max Depth = 68
- Call Chain = USBD_StdEPReq ⇒ USBD_CtlSendData ⇒ USBD_LL_Transmit ⇒ HAL_PCD_EP_Transmit ⇒ PCD_WritePMA

[Calls]

- >> USBD_LL_StallEP
- >> USBD_LL_IsStallEP
- >> USBD_LL_ClearStallEP
- >> USBD_CtlSendData
- >> USBD_CtlError
- >> USBD_CtlSendStatus

[Called By]

- >> USBD_LL_SetupStage

USBD_StdItfReq (Thumb, 58 bytes, Stack size 16 bytes, usbd_ctlreq.o(i.USBD_StdItfReq))

[Stack]

- Max Depth = 60
- Call Chain = USBD_StdItfReq ⇒ USBD_CtlSendStatus ⇒ USBD_LL_Transmit ⇒ HAL_PCD_EP_Transmit ⇒ PCD_WritePMA

[Calls]

- >> USBD_CtlError
- >> USBD_CtlSendStatus

[Called By]

- >> USBD_LL_SetupStage

USBD_static_free (Thumb, 2 bytes, Stack size 0 bytes, usbd_conf.o(i.USBD_static_free))

[Called By]

- >> USBD_HID_DeInit

USBD_static_malloc (Thumb, 4 bytes, Stack size 0 bytes, usbd_conf.o(i.USBD_static_malloc))

[Called By]

- >> USBD_HID_Init

USB_IRQHandler (Thumb, 10 bytes, Stack size 8 bytes, stm32f0xx_it.o(i.USB_IRQHandler))

[Stack]

- Max Depth = 220
- Call Chain = USB_IRQHandler ⇒ HAL_PCD_IRQHandler ⇒ HAL_PCD_ResumeCallback ⇒ SystemClock_Config ⇒ HAL_RCC_ClockConfig ⇒ HAL_RCC_GetSysClockFreq ⇒ __aeabi_uidivmod

[Calls]

- >> HAL_PCD_IRQHandler

[Address Reference Count : 1]

- startup_stm32f042x6.o(RESET)

_Error_Handler (Thumb, 2 bytes, Stack size 0 bytes, main.o(i._Error_Handler))

[Calls]

- >> _Error_Handler

[Called By]

- >> USBD_LL_Init
- >> _Error_Handler

__0printf$5 (Thumb, 24 bytes, Stack size 24 bytes, printf5.o(i.__0printf$5), UNUSED)

[Calls]

- >> _printf_core

__1printf$5 (Thumb, 0 bytes, Stack size 24 bytes, printf5.o(i.__0printf$5), UNUSED)

__2printf (Thumb, 0 bytes, Stack size 24 bytes, printf5.o(i.__0printf$5))

[Stack]

- Max Depth = 24
- Call Chain = __2printf

[Called By]

- >> main

__ARM_common_switch8 (Thumb, 26 bytes, Stack size 8 bytes, stm32f0xx_hal_dma.o(i.__ARM_common_switch8))

[Stack]

- Max Depth = 8
- Call Chain = __ARM_common_switch8

[Called By]

- >> USBD_GetDescriptor
- >> USBD_StdDevReq

__scatterload_copy (Thumb, 14 bytes, Stack size unknown bytes, handlers.o(i.__scatterload_copy), UNUSED)

__scatterload_null (Thumb, 2 bytes, Stack size unknown bytes, handlers.o(i.__scatterload_null), UNUSED)

__scatterload_zeroinit (Thumb, 14 bytes, Stack size unknown bytes, handlers.o(i.__scatterload_zeroinit), UNUSED)

fputc (Thumb, 18 bytes, Stack size 16 bytes, main.o(i.fputc))

[Stack]

- Max Depth = 104
- Call Chain = fputc ⇒ HAL_UART_Transmit ⇒ UART_WaitOnFlagUntilTimeout

[Calls]

- >> HAL_UART_Transmit

[Address Reference Count : 1]

- printf5.o(i.__0printf$5)

main (Thumb, 136 bytes, Stack size 0 bytes, main.o(i.main))

[Stack]

- Max Depth = 188
- Call Chain = main ⇒ SystemClock_Config ⇒ HAL_RCC_ClockConfig ⇒ HAL_RCC_GetSysClockFreq ⇒ __aeabi_uidivmod

[Calls]

- >> MX_USB_DEVICE_Init
- >> HAL_Init
- >> SystemClock_Config
- >> MX_USART2_UART_Init
- >> MX_SPI1_Init
- >> MX_GPIO_Init
- >> HAL_GPIO_WritePin
- >> nrf24_tx_address
- >> nrf24_rx_address
- >> nrf24_init
- >> nrf24_getData
- >> nrf24_dataReady
- >> nrf24_config
- >> __2printf

[Address Reference Count : 1]

- entry9a.o(.ARM.Collect$$$$0000000B)

nrf24_ce_digitalWrite (Thumb, 24 bytes, Stack size 8 bytes, radiopinfunctions.o(i.nrf24_ce_digitalWrite))

[Stack]

- Max Depth = 8
- Call Chain = nrf24_ce_digitalWrite

[Calls]

- >> HAL_GPIO_WritePin

[Called By]

- >> nrf24_rx_address
- >> nrf24_powerUpRx
- >> nrf24_init

nrf24_config (Thumb, 116 bytes, Stack size 8 bytes, nrf24.o(i.nrf24_config))

[Stack]

- Max Depth = 144
- Call Chain = nrf24_config ⇒ nrf24_powerUpRx ⇒ nrf24_configRegister ⇒ spi_transfer ⇒ HAL_SPI_TransmitReceive ⇒ SPI_EndRxTxTransaction ⇒ SPI_WaitFlagStateUntilTimeout

[Calls]

- >> nrf24_powerUpRx
- >> nrf24_configRegister

[Called By]

- >> main

nrf24_configRegister (Thumb, 36 bytes, Stack size 16 bytes, nrf24.o(i.nrf24_configRegister))

[Stack]

- Max Depth = 128
- Call Chain = nrf24_configRegister ⇒ spi_transfer ⇒ HAL_SPI_TransmitReceive ⇒ SPI_EndRxTxTransaction ⇒ SPI_WaitFlagStateUntilTimeout

[Calls]

- >> nrf24_csn_digitalWrite
- >> spi_transfer

[Called By]

- >> nrf24_powerUpRx
- >> nrf24_getData
- >> nrf24_config

nrf24_csn_digitalWrite (Thumb, 26 bytes, Stack size 8 bytes, radiopinfunctions.o(i.nrf24_csn_digitalWrite))

[Stack]

- Max Depth = 8
- Call Chain = nrf24_csn_digitalWrite

[Calls]

- >> HAL_GPIO_WritePin

[Called By]

- >> nrf24_writeRegister
- >> nrf24_readRegister
- >> nrf24_powerUpRx
- >> nrf24_init
- >> nrf24_getStatus
- >> nrf24_getData
- >> nrf24_configRegister

nrf24_dataReady (Thumb, 26 bytes, Stack size 8 bytes, nrf24.o(i.nrf24_dataReady))

[Stack]

- Max Depth = 168
- Call Chain = nrf24_dataReady ⇒ nrf24_rxFifoEmpty ⇒ nrf24_readRegister ⇒ nrf24_transferSync ⇒ spi_transfer ⇒ HAL_SPI_TransmitReceive ⇒ SPI_EndRxTxTransaction ⇒ SPI_WaitFlagStateUntilTimeout

[Calls]

- >> nrf24_rxFifoEmpty
- >> nrf24_getStatus

[Called By]

- >> main

nrf24_getData (Thumb, 44 bytes, Stack size 8 bytes, nrf24.o(i.nrf24_getData))

[Stack]

- Max Depth = 144
- Call Chain = nrf24_getData ⇒ nrf24_transferSync ⇒ spi_transfer ⇒ HAL_SPI_TransmitReceive ⇒ SPI_EndRxTxTransaction ⇒ SPI_WaitFlagStateUntilTimeout

[Calls]

- >> nrf24_csn_digitalWrite
- >> spi_transfer
- >> nrf24_transferSync
- >> nrf24_configRegister

[Called By]

- >> main

nrf24_getStatus (Thumb, 26 bytes, Stack size 8 bytes, nrf24.o(i.nrf24_getStatus))

[Stack]

- Max Depth = 120
- Call Chain = nrf24_getStatus ⇒ spi_transfer ⇒ HAL_SPI_TransmitReceive ⇒ SPI_EndRxTxTransaction ⇒ SPI_WaitFlagStateUntilTimeout

[Calls]

- >> nrf24_csn_digitalWrite
- >> spi_transfer

[Called By]

- >> nrf24_dataReady

nrf24_init (Thumb, 16 bytes, Stack size 8 bytes, nrf24.o(i.nrf24_init))

[Stack]

- Max Depth = 16
- Call Chain = nrf24_init ⇒ nrf24_csn_digitalWrite

[Calls]

- >> nrf24_csn_digitalWrite
- >> nrf24_ce_digitalWrite

[Called By]

- >> main

nrf24_powerUpRx (Thumb, 50 bytes, Stack size 8 bytes, nrf24.o(i.nrf24_powerUpRx))

[Stack]

- Max Depth = 136
- Call Chain = nrf24_powerUpRx ⇒ nrf24_configRegister ⇒ spi_transfer ⇒ HAL_SPI_TransmitReceive ⇒ SPI_EndRxTxTransaction ⇒ SPI_WaitFlagStateUntilTimeout

[Calls]

- >> nrf24_csn_digitalWrite
- >> nrf24_ce_digitalWrite
- >> spi_transfer
- >> nrf24_configRegister

[Called By]

- >> nrf24_config

nrf24_readRegister (Thumb, 40 bytes, Stack size 16 bytes, nrf24.o(i.nrf24_readRegister))

[Stack]

- Max Depth = 152
- Call Chain = nrf24_readRegister ⇒ nrf24_transferSync ⇒ spi_transfer ⇒ HAL_SPI_TransmitReceive ⇒ SPI_EndRxTxTransaction ⇒ SPI_WaitFlagStateUntilTimeout

[Calls]

- >> nrf24_csn_digitalWrite
- >> spi_transfer
- >> nrf24_transferSync

[Called By]

- >> nrf24_rxFifoEmpty

nrf24_rxFifoEmpty (Thumb, 22 bytes, Stack size 8 bytes, nrf24.o(i.nrf24_rxFifoEmpty))

[Stack]

- Max Depth = 160
- Call Chain = nrf24_rxFifoEmpty ⇒ nrf24_readRegister ⇒ nrf24_transferSync ⇒ spi_transfer ⇒ HAL_SPI_TransmitReceive ⇒ SPI_EndRxTxTransaction ⇒ SPI_WaitFlagStateUntilTimeout

[Calls]

- >> nrf24_readRegister

[Called By]

- >> nrf24_dataReady

nrf24_rx_address (Thumb, 28 bytes, Stack size 8 bytes, nrf24.o(i.nrf24_rx_address))

[Stack]

- Max Depth = 152
- Call Chain = nrf24_rx_address ⇒ nrf24_writeRegister ⇒ nrf24_transmitSync ⇒ spi_transfer ⇒ HAL_SPI_TransmitReceive ⇒ SPI_EndRxTxTransaction ⇒ SPI_WaitFlagStateUntilTimeout

[Calls]

- >> nrf24_ce_digitalWrite
- >> nrf24_writeRegister

[Called By]

- >> main

nrf24_transferSync (Thumb, 30 bytes, Stack size 24 bytes, nrf24.o(i.nrf24_transferSync))

[Stack]

- Max Depth = 136
- Call Chain = nrf24_transferSync ⇒ spi_transfer ⇒ HAL_SPI_TransmitReceive ⇒ SPI_EndRxTxTransaction ⇒ SPI_WaitFlagStateUntilTimeout

[Calls]

- >> spi_transfer

[Called By]

- >> nrf24_readRegister
- >> nrf24_getData

nrf24_transmitSync (Thumb, 26 bytes, Stack size 16 bytes, nrf24.o(i.nrf24_transmitSync))

[Stack]

- Max Depth = 128
- Call Chain = nrf24_transmitSync ⇒ spi_transfer ⇒ HAL_SPI_TransmitReceive ⇒ SPI_EndRxTxTransaction ⇒ SPI_WaitFlagStateUntilTimeout

[Calls]

- >> spi_transfer

[Called By]

- >> nrf24_writeRegister

nrf24_tx_address (Thumb, 26 bytes, Stack size 8 bytes, nrf24.o(i.nrf24_tx_address))

[Stack]

- Max Depth = 152
- Call Chain = nrf24_tx_address ⇒ nrf24_writeRegister ⇒ nrf24_transmitSync ⇒ spi_transfer ⇒ HAL_SPI_TransmitReceive ⇒ SPI_EndRxTxTransaction ⇒ SPI_WaitFlagStateUntilTimeout

[Calls]

- >> nrf24_writeRegister

[Called By]

- >> main

nrf24_writeRegister (Thumb, 40 bytes, Stack size 16 bytes, nrf24.o(i.nrf24_writeRegister))

[Stack]

- Max Depth = 144
- Call Chain = nrf24_writeRegister ⇒ nrf24_transmitSync ⇒ spi_transfer ⇒ HAL_SPI_TransmitReceive ⇒ SPI_EndRxTxTransaction ⇒ SPI_WaitFlagStateUntilTimeout

[Calls]

- >> nrf24_csn_digitalWrite
- >> spi_transfer
- >> nrf24_transmitSync

[Called By]

- >> nrf24_tx_address
- >> nrf24_rx_address

spi_transfer (Thumb, 32 bytes, Stack size 16 bytes, nrf24.o(i.spi_transfer))

[Stack]

- Max Depth = 112
- Call Chain = spi_transfer ⇒ HAL_SPI_TransmitReceive ⇒ SPI_EndRxTxTransaction ⇒ SPI_WaitFlagStateUntilTimeout

[Calls]

- >> HAL_SPI_TransmitReceive

[Called By]

- >> nrf24_writeRegister
- >> nrf24_transmitSync
- >> nrf24_transferSync
- >> nrf24_readRegister
- >> nrf24_powerUpRx
- >> nrf24_getStatus
- >> nrf24_getData
- >> nrf24_configRegister

### Local Symbols

MX_GPIO_Init (Thumb, 174 bytes, Stack size 48 bytes, main.o(i.MX_GPIO_Init))

[Stack]

- Max Depth = 72
- Call Chain = MX_GPIO_Init ⇒ HAL_GPIO_Init

[Calls]

- >> HAL_GPIO_Init
- >> HAL_GPIO_WritePin

[Called By]

- >> main

MX_SPI1_Init (Thumb, 66 bytes, Stack size 8 bytes, main.o(i.MX_SPI1_Init))

[Stack]

- Max Depth = 88
- Call Chain = MX_SPI1_Init ⇒ HAL_SPI_Init ⇒ HAL_SPI_MspInit ⇒ HAL_GPIO_Init

[Calls]

- >> HAL_SPI_Init

[Called By]

- >> main

MX_USART2_UART_Init (Thumb, 46 bytes, Stack size 8 bytes, main.o(i.MX_USART2_UART_Init))

[Stack]

- Max Depth = 108
- Call Chain = MX_USART2_UART_Init ⇒ HAL_HalfDuplex_Init ⇒ UART_SetConfig ⇒ HAL_RCC_GetSysClockFreq ⇒ __aeabi_uidivmod

[Calls]

- >> HAL_HalfDuplex_Init

[Called By]

- >> main

PCD_EP_ISR_Handler (Thumb, 802 bytes, Stack size 40 bytes, stm32f0xx_hal_pcd.o(i.PCD_EP_ISR_Handler))

[Stack]

- Max Depth = 156
- Call Chain = PCD_EP_ISR_Handler ⇒ HAL_PCD_SetupStageCallback ⇒ USBD_LL_SetupStage ⇒ USBD_StdDevReq ⇒ USBD_GetDescriptor ⇒ USBD_CtlSendData ⇒ USBD_LL_Transmit ⇒ HAL_PCD_EP_Transmit ⇒ PCD_WritePMA

[Calls]

- >> HAL_PCD_EP_Transmit
- >> HAL_PCD_EP_Receive
- >> HAL_PCD_SetupStageCallback
- >> HAL_PCD_DataOutStageCallback
- >> HAL_PCD_DataInStageCallback
- >> PCD_WritePMA
- >> PCD_ReadPMA

[Called By]

- >> HAL_PCD_IRQHandler

SPI_EndRxTxTransaction (Thumb, 76 bytes, Stack size 24 bytes, stm32f0xx_hal_spi.o(i.SPI_EndRxTxTransaction))

[Stack]

- Max Depth = 48
- Call Chain = SPI_EndRxTxTransaction ⇒ SPI_WaitFlagStateUntilTimeout

[Calls]

- >> SPI_WaitFlagStateUntilTimeout
- >> SPI_WaitFifoStateUntilTimeout

[Called By]

- >> HAL_SPI_TransmitReceive

SPI_WaitFifoStateUntilTimeout (Thumb, 150 bytes, Stack size 24 bytes, stm32f0xx_hal_spi.o(i.SPI_WaitFifoStateUntilTimeout))

[Stack]

- Max Depth = 24
- Call Chain = SPI_WaitFifoStateUntilTimeout

[Calls]

- >> HAL_GetTick

[Called By]

- >> SPI_EndRxTxTransaction

SPI_WaitFlagStateUntilTimeout (Thumb, 140 bytes, Stack size 24 bytes, stm32f0xx_hal_spi.o(i.SPI_WaitFlagStateUntilTimeout))

[Stack]

- Max Depth = 24
- Call Chain = SPI_WaitFlagStateUntilTimeout

[Calls]

- >> HAL_GetTick

[Called By]

- >> SPI_EndRxTxTransaction

NVIC_SetPriority (Thumb, 60 bytes, Stack size 0 bytes, stm32f0xx_hal_cortex.o(i.NVIC_SetPriority))

[Called By]

- >> HAL_SYSTICK_Config
- >> HAL_NVIC_SetPriority

USBD_GetDescriptor (Thumb, 224 bytes, Stack size 24 bytes, usbd_ctlreq.o(i.USBD_GetDescriptor))

[Stack]

- Max Depth = 68
- Call Chain = USBD_GetDescriptor ⇒ USBD_CtlSendData ⇒ USBD_LL_Transmit ⇒ HAL_PCD_EP_Transmit ⇒ PCD_WritePMA

[Calls]

- >> USBD_CtlSendData
- >> USBD_CtlError
- >> __ARM_common_switch8

[Called By]

- >> USBD_StdDevReq

USBD_SetConfig (Thumb, 108 bytes, Stack size 16 bytes, usbd_ctlreq.o(i.USBD_SetConfig))

[Stack]

- Max Depth = 60
- Call Chain = USBD_SetConfig ⇒ USBD_CtlSendStatus ⇒ USBD_LL_Transmit ⇒ HAL_PCD_EP_Transmit ⇒ PCD_WritePMA

[Calls]

- >> USBD_CtlError
- >> USBD_CtlSendStatus
- >> USBD_SetClassConfig
- >> USBD_ClrClassConfig

[Called By]

- >> USBD_StdDevReq

USBD_HID_DataIn (Thumb, 16 bytes, Stack size 0 bytes, usbd_hid.o(i.USBD_HID_DataIn))
[Address Reference Count : 1]

- usbd_hid.o(.data)

USBD_HID_DeInit (Thumb, 34 bytes, Stack size 8 bytes, usbd_hid.o(i.USBD_HID_DeInit))

[Stack]

- Max Depth = 36
- Call Chain = USBD_HID_DeInit ⇒ USBD_LL_CloseEP ⇒ HAL_PCD_EP_Close

[Calls]

- >> USBD_static_free
- >> USBD_LL_CloseEP

[Address Reference Count : 1]

- usbd_hid.o(.data)

USBD_HID_GetCfgDesc (Thumb, 8 bytes, Stack size 0 bytes, usbd_hid.o(i.USBD_HID_GetCfgDesc))
[Address Reference Count : 1]

- usbd_hid.o(.data)

USBD_HID_GetDeviceQualifierDesc (Thumb, 8 bytes, Stack size 0 bytes, usbd_hid.o(i.USBD_HID_GetDeviceQualifierDesc))
[Address Reference Count : 1]

- usbd_hid.o(.data)

USBD_HID_Init (Thumb, 46 bytes, Stack size 16 bytes, usbd_hid.o(i.USBD_HID_Init))

[Stack]

- Max Depth = 52
- Call Chain = USBD_HID_Init ⇒ USBD_LL_OpenEP ⇒ HAL_PCD_EP_Open

[Calls]

- >> USBD_static_malloc
- >> USBD_LL_OpenEP

[Address Reference Count : 1]

- usbd_hid.o(.data)

USBD_HID_Setup (Thumb, 154 bytes, Stack size 16 bytes, usbd_hid.o(i.USBD_HID_Setup))

[Stack]

- Max Depth = 60
- Call Chain = USBD_HID_Setup ⇒ USBD_CtlSendData ⇒ USBD_LL_Transmit ⇒ HAL_PCD_EP_Transmit ⇒ PCD_WritePMA

[Calls]

- >> USBD_CtlSendData
- >> USBD_CtlError

[Address Reference Count : 1]

- usbd_hid.o(.data)

_printf_core (Thumb, 688 bytes, Stack size 96 bytes, printf5.o(i._printf_core), UNUSED)

[Calls]

- >> __aeabi_uldivmod

[Called By]

- >> __0printf$5

### Undefined Global Symbols
