dekuNukem/daytripper/pcb/rev3/rx.brd

## EAGLE design pcb/rev3/rx.brd (2019-02-25, an earlier design)

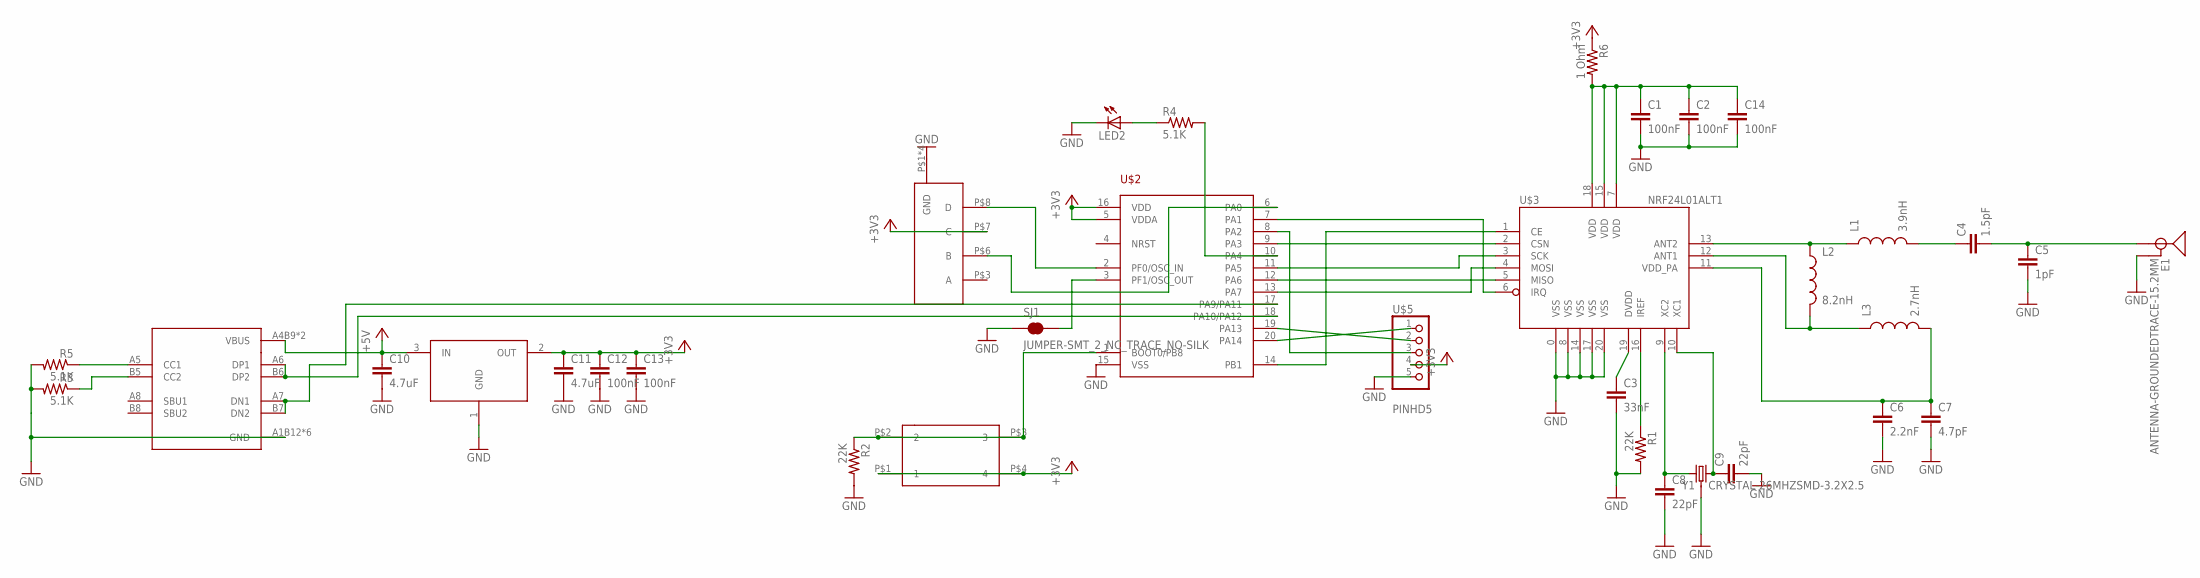
[picture p66: schematic rx.sch]

Parts:
C1, C2, C12, C13, C14: 100nF; 0805
C3: 33nF; 0805
C4: 1.5pF; 0805
C5: 1pF; 0805
C6: 2.2nF; 0805
C7: 4.7pF; 0805
C8, C9: 22pF; 0805
C10, C11: 4.7uF; 0805
E1: ANTENNA-GROUNDEDTRACE-15.2MM; TRACE_ANTENNA_2.4GHZ_15.2MM
L1: 3.9nH; 0805
L2: 8.2nH; 0805
L3: 2.7nH; 0805
LED2: LEDCHIP-LED0805; CHIP-LED0805
R1, R2: 22K; 0805
R3, R4, R5: 5.1K; 0805
R6: 1 Ohm; 0805
SJ1: JUMPER-SMT_2_NC_TRACE_NO-SILK; SMT-JUMPER_2_NC_TRACE_NO-SILK
U$1: SW_3POS_DEVSW_3POS_OFFICIAL; SW_3POS_FOOT_OFFICIAL
U$2: STM32F042F4; TSSOP20
U$3: NRF24L01ALT1; QFN20_ALT1
U$4: XC6206_DEV; SOT23R_INFINEON
U$5: PINHD5; 1X05
U$6: USBC_16P; USBC_16P_FOOT
U$10: 324_SW324_SWITCH_FOOT_HOLE; 342_SWICH_FOOT_HOLE
Y1: CRYSTAL-26MHZSMD-3.2X2.5; CRYSTAL-SMD-3.2X2.5MM

Connections:
+3V3: C11.1, C12.1, C13.1, R6.1, U$1.P$7 (C), U$2.5 (VDDA), U$2.16 (VDD), U$4.2 (OUT), U$5.4, U$10.P$1 (1), U$10.P$4 (4)
+5V: C10.1, U$4.3 (IN), U$6.A4B9 (VBUS), U$6.B4A9 (VBUS)
GND: C1.2, C2.2, C3.2, C5.2, C6.2, C7.2, C8.2, C9.2, C10.2, C11.2, C12.2, C13.2, C14.2, E1.GND, LED2.C, R1.2, R2.2, R3.2, R5.2, SJ1.1, U$1.P$1 (GND), U$1.P$2 (GND), U$1.P$4 (GND), U$1.P$5 (GND), U$2.15 (VSS), U$3.0 (VSS), U$3.8 (VSS), U$3.14 (VSS), U$3.17 (VSS), U$3.20 (VSS), U$4.1 (GND), U$5.5, U$6.A1B12 (GND), U$6.B11A12 (GND), U$6.P$13 (GND), U$6.P$14 (GND), U$6.P$15 (GND), U$6.P$16 (GND), Y1.2 (3), Y1.4 (3)
unnamed: C3.1, U$3.19 (DVDD)
unnamed: R1.1, U$3.16 (IREF)
unnamed: L1.1, L2.1, U$3.13 (ANT2)
unnamed: C4.1, L1.2
unnamed: C4.2, C5.1, E1.ANT (SIGNAL)
unnamed: L2.2, L3.1, U$3.12 (ANT1)
unnamed: C8.1, U$3.9 (XC2), Y1.1
unnamed: C6.1, C7.1, L3.2, U$3.11 (VDD_PA)
unnamed: C9.1, U$3.10 (XC1), Y1.3 (2)
unnamed: U$1.P$8 (D), U$2.2 (PF0/OSC_IN)
unnamed: R2.1, U$2.1 (BOOT0/PB8), U$10.P$2 (2), U$10.P$3 (3)
unnamed: U$2.17 (PA9/PA11), U$6.A7 (DN1), U$6.B7 (DN2)
unnamed: U$2.18 (PA10/PA12), U$6.A6 (DP1), U$6.B6 (DP2)
unnamed: U$2.12 (PA6), U$3.5 (MISO)
unnamed: U$2.13 (PA7), U$3.4 (MOSI)
unnamed: U$2.11 (PA5), U$3.3 (SCK)
unnamed: U$2.19 (PA13), U$5.2
unnamed: LED2.A, R4.1
unnamed: SJ1.2, U$2.3 (PF1/OSC_OUT)
unnamed: U$2.20 (PA14), U$5.1
unnamed: U$2.8 (PA2), U$5.3
unnamed: U$2.14 (PB1), U$3.1 (CE)
unnamed: R4.2, U$2.10 (PA4)
unnamed: U$2.9 (PA3), U$3.2 (CSN)
unnamed: R3.1, U$6.B5 (CC2)
unnamed: U$1.P$6 (B), U$2.6 (PA0)
unnamed: R5.1, U$6.A5 (CC1)
unnamed: C1.1, C2.1, C14.1, R6.2, U$3.7 (VDD), U$3.15 (VDD), U$3.18 (VDD)
unnamed: U$2.7 (PA1), U$3.6 (IRQ)

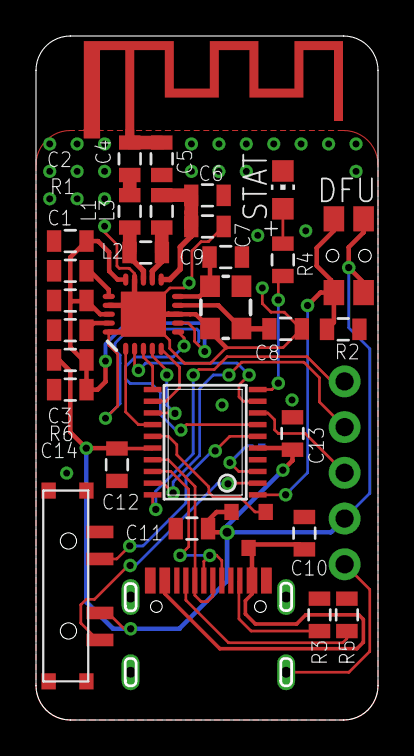
[picture p67: board pcb/rev3/rx.brd from above]

Board: 2 copper layers, 19.0 x 38.0 mm, 34 parts (1 on the bottom side), 32 nets.
