dekuNukem/daytripper/pcb/misc/rxSD.brd

## EAGLE design pcb/misc/rxSD.brd (2018-10-05)

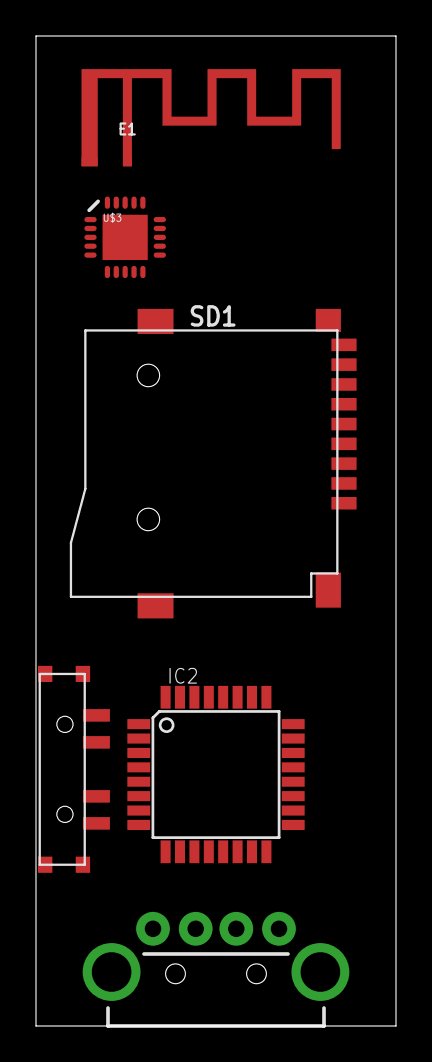
[picture p68: board rxSD.brd from above]

Board: 2 copper layers, 20.0 x 55.0 mm, 6 parts (0 on the bottom side), 2 nets, no tracks yet.

Parts:
E1: ANTENNA-GROUNDEDTRACE-15.2MM; TRACE_ANTENNA_2.4GHZ_15.2MM
IC2: STM32F042K6; TQFP32-08
J1: USB_A_PTH_MALE; USB-A-H
SD1: TF-HOLDER; TF-PULL
U$1: SW_3POS_DEVSW_3POS_OFFICIAL; SW_3POS_FOOT_OFFICIAL
U$3: NRF24L01ALT1; QFN20_ALT1

Connections:
VDD: SD1.4, U$3.7, U$3.15, U$3.18
VSS: SD1.6, U$3.0, U$3.8, U$3.14, U$3.17, U$3.20
