dekuNukem/daytripper/pcb/misc/rx.brd

## EAGLE design pcb/misc/rx.brd (2018-10-15)

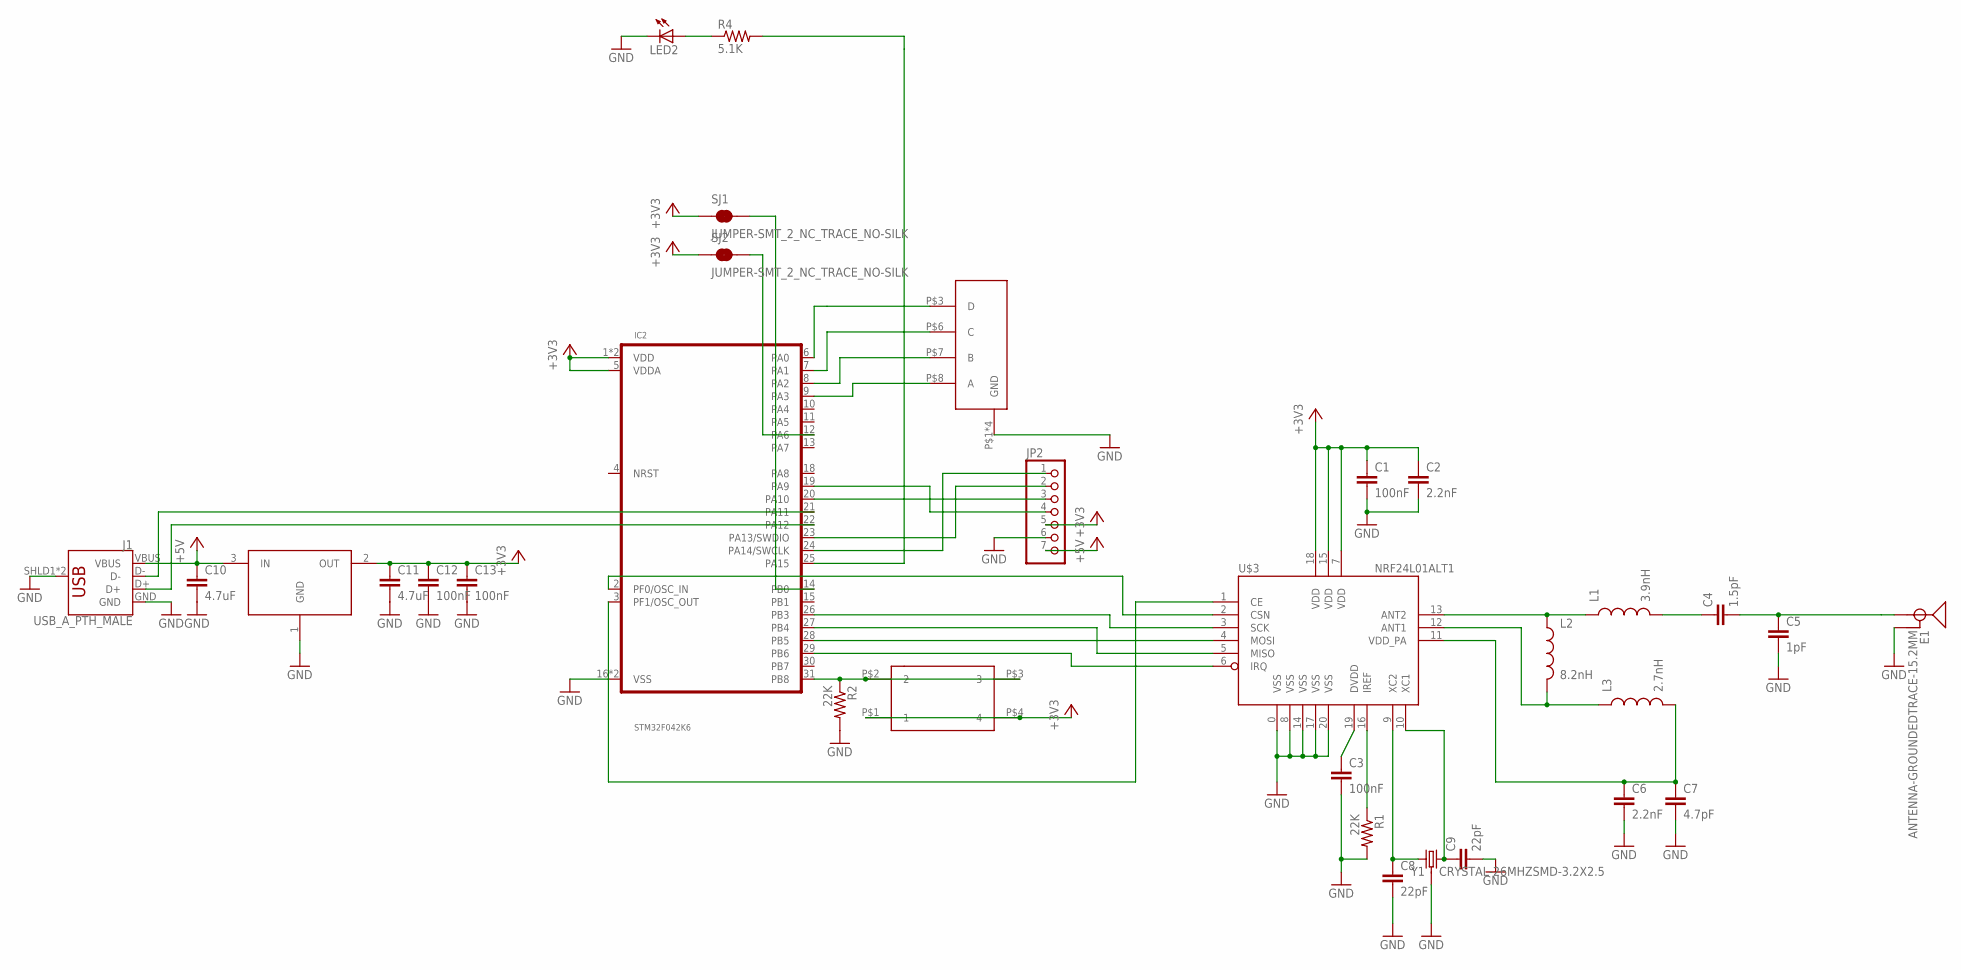
[picture p69: schematic rx.sch]

Parts:
C1, C3, C12, C13: 100nF; 0805
C2, C6: 2.2nF; 0805
C4: 1.5pF; 0805
C5: 1pF; 0805
C7: 4.7pF; 0805
C8, C9: 22pF; 0805
C10, C11: 4.7uF; 0805
E1: ANTENNA-GROUNDEDTRACE-15.2MM; TRACE_ANTENNA_2.4GHZ_15.2MM
IC2: STM32F042K6; TQFP32-08
J1: USB_A_PTH_MALE; USB-A-H
JP2: PINHD-1X8CLEANBIG; 1X08-CLEANBIG
L1: 3.9nH; 0805
L2: 8.2nH; 0805
L3: 2.7nH; 0805
LED2: LEDCHIP-LED0805; CHIP-LED0805
R1, R2: 22K; 0805
R4: 5.1K; 0805
SJ1, SJ2: JUMPER-SMT_2_NC_TRACE_NO-SILK; SMT-JUMPER_2_NC_TRACE_NO-SILK
U$1: SW_3POS_DEVSW_3POS_OFFICIAL; SW_3POS_FOOT_OFFICIAL
U$3: NRF24L01ALT1; QFN20_ALT1
U$4: XC6206_DEV; SOT23R_INFINEON
U$10: 324_SW; 342_SWICH_FOOT
Y1: CRYSTAL-26MHZSMD-3.2X2.5; CRYSTAL-SMD-3.2X2.5MM

Connections:
+3V3: C1.1, C2.1, C11.1, C12.1, C13.1, IC2.1 (VDD), IC2.5 (VDDA), IC2.17 (VDD), JP2.5, SJ1.1, SJ2.1, U$3.7 (VDD), U$3.15 (VDD), U$3.18 (VDD), U$4.2 (OUT), U$10.P$1 (1), U$10.P$4 (4)
+5V: C10.1, J1.VBUS, JP2.7, U$4.3 (IN)
GND: C1.2, C2.2, C3.2, C5.2, C6.2, C7.2, C8.2, C9.2, C10.2, C11.2, C12.2, C13.2, E1.GND, IC2.16 (VSS), IC2.32 (VSS), J1.GND, J1.SHLD1 (SHIELD), J1.SHLD2 (SHIELD), JP2.6, LED2.C, R1.2, R2.2, U$1.P$1 (GND), U$1.P$2 (GND), U$1.P$4 (GND), U$1.P$5 (GND), U$3.0 (VSS), U$3.8 (VSS), U$3.14 (VSS), U$3.17 (VSS), U$3.20 (VSS), U$4.1 (GND), Y1.2 (3), Y1.4 (3)
unnamed: C3.1, U$3.19 (DVDD)
unnamed: R1.1, U$3.16 (IREF)
unnamed: L1.1, L2.1, U$3.13 (ANT2)
unnamed: C4.1, L1.2
unnamed: C4.2, C5.1, E1.ANT (SIGNAL)
unnamed: L2.2, L3.1, U$3.12 (ANT1)
unnamed: C8.1, U$3.9 (XC2), Y1.1
unnamed: C6.1, C7.1, L3.2, U$3.11 (VDD_PA)
unnamed: C9.1, U$3.10 (XC1), Y1.3 (2)
unnamed: IC2.6 (PA0), U$1.P$3 (D)
unnamed: IC2.31 (PB8), R2.1, U$10.P$2 (2), U$10.P$3 (3)
unnamed: IC2.21 (PA11), J1.D-
unnamed: IC2.22 (PA12), J1.D+
unnamed: IC2.28 (PB5), U$3.4 (MOSI)
unnamed: IC2.27 (PB4), U$3.5 (MISO)
unnamed: IC2.26 (PB3), U$3.3 (SCK)
unnamed: IC2.29 (PB6), U$3.6 (IRQ)
unnamed: LED2.A, R4.1
unnamed: IC2.2 (PF0/OSC_IN), U$3.2 (CSN)
unnamed: IC2.3 (PF1/OSC_OUT), U$3.1 (CE)
unnamed: IC2.24 (PA14/SWCLK), JP2.1
unnamed: IC2.23 (PA13/SWDIO), JP2.2
unnamed: IC2.20 (PA10), JP2.3
unnamed: IC2.19 (PA9), JP2.4
unnamed: IC2.7 (PA1), U$1.P$6 (C)
unnamed: IC2.8 (PA2), U$1.P$7 (B)
unnamed: IC2.9 (PA3), U$1.P$8 (A)
unnamed: IC2.25 (PA15), R4.2
unnamed: IC2.12 (PA6), SJ2.2
unnamed: IC2.14 (PB0), SJ1.2
