dekuNukem/daytripper/pcb/misc/rx.brd

## EAGLE design pcb/misc/rx.brd (continued)

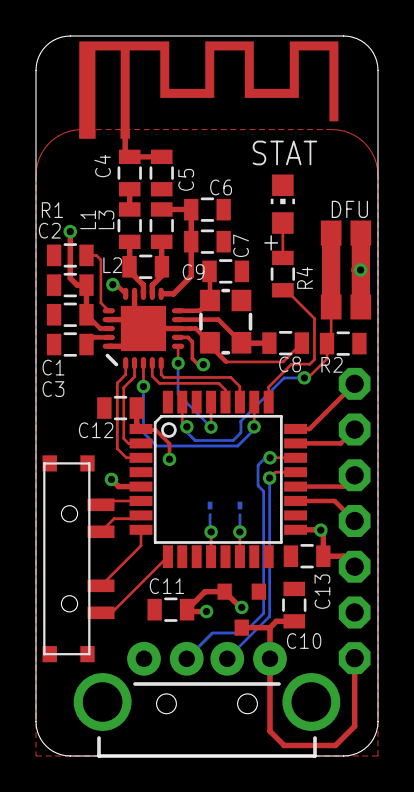
[picture p70: board pcb/misc/rx.brd from above]

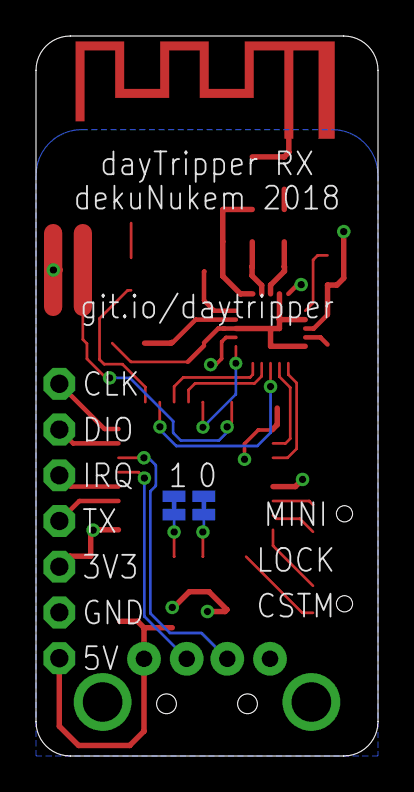
[picture p71: board pcb/misc/rx.brd from below]

Board: 2 copper layers, 19.0 x 40.0 mm, 31 parts (2 on the bottom side), 33 nets.
