dekuNukem/daytripper/pcb/misc/nRF24L01-Chip-v13/nRF24L01-Chip-v13.brd

## EAGLE design pcb/misc/nRF24L01-Chip-v13/nRF24L01-Chip-v13.brd (2018-08-13)

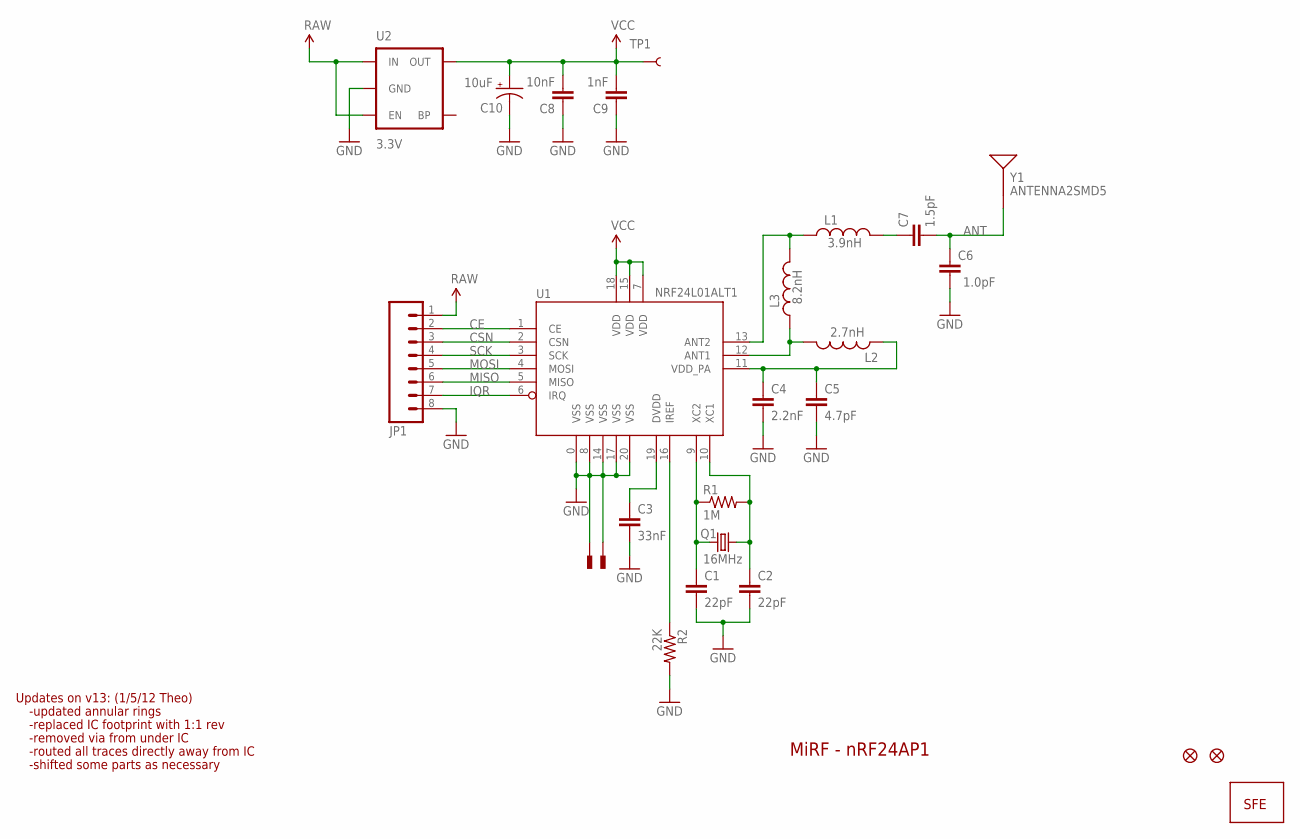
[picture p72: schematic nRF24L01-Chip-v13.sch]

Parts:
C1, C2: 22pF; 0402-CAP
C3: 33nF; 0402-CAP
C4: 2.2nF; 0402-CAP
C5: 4.7pF; 0402-CAP
C6: 1.0pF; 0402-CAP
C7: 1.5pF; 0402-CAP
C8: 10nF; 0402-CAP
C9: 1nF; 0402-CAP
C10: 10uF; EIA3216
JP1: M081X08; 1X08
JP2, JP3: FIDUCIALUFIDUCIAL; MICRO-FIDUCIAL
L1: 3.9nH; C0402
L2: 2.7nH; C0402
L3: 8.2nH; C0402
Q1: 16MHz; CRYSTAL-SMD-5X3
R1: 1M; 0402-RES
R2: 22K; 0402-RES
TP1: TEST-POINT3X5; PAD.03X.05
U1: NRF24L01ALT1; QFN20_ALT1
U2: 3.3V; SOT23-5
U$1, U$4: PAD; PAD-0.008
U$5: LOGO-SFENEW; SFE-NEW-WEBLOGO
Y1: ANTENNA2SMD5; ANTENNA-CHIP5

Connections:
ANT: C6.2, C7.2, Y1.FEED
CE: JP1.2, U1.1 (CE)
CSN: JP1.3, U1.2 (CSN)
GND: C1.2, C2.2, C3.2, C4.2, C5.2, C6.1, C8.1, C9.1, C10.C (-), JP1.8, R2.2, U1.0 (VSS), U1.8 (VSS), U1.14 (VSS), U1.17 (VSS), U1.20 (VSS), U2.2 (GND), U$1.P$1, U$4.P$1
IQR: JP1.7, U1.6 (IRQ)
MISO: JP1.6, U1.5 (MISO)
MOSI: JP1.5, U1.4 (MOSI)
unnamed: C1.1, Q1.1, R1.1, U1.9 (XC2)
unnamed: C2.1, Q1.3 (2), R1.2, U1.10 (XC1)
unnamed: L2.2, L3.1, U1.12 (ANT1)
unnamed: R2.1, U1.16 (IREF)
unnamed: C3.1, U1.19 (DVDD)
unnamed: L1.1, L3.2, U1.13 (ANT2)
unnamed: C4.1, C5.1, L2.1, U1.11 (VDD_PA)
unnamed: C7.1, L1.2
RAW: JP1.1, U2.1 (IN), U2.3 (EN)
SCK: JP1.4, U1.3 (SCK)
VCC: C8.2, C9.2, C10.A (+), TP1.P$1, U1.7 (VDD), U1.15 (VDD), U1.18 (VDD), U2.5 (OUT)

Notes on the sheet:
MiRF - nRF24AP1
Updates on v13: (1/5/12 Theo)
-updated annular rings
-replaced IC footprint with 1:1 rev
-removed via from under IC
-routed all traces directly away from IC
-shifted some parts as necessary

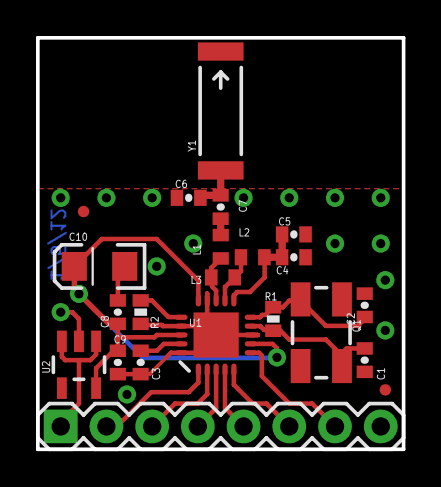
[picture p73: board nRF24L01-Chip-v13.brd from above]

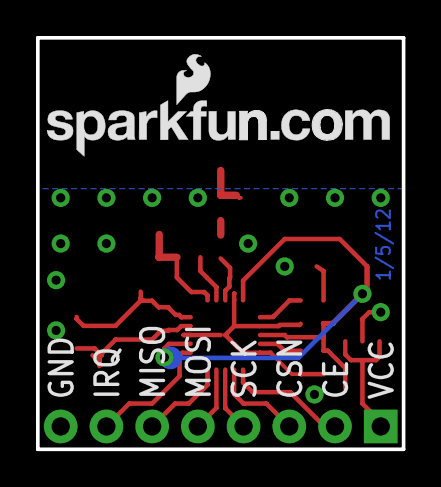
[picture p74: board nRF24L01-Chip-v13.brd from below]

Board: 2 copper layers, 20.3 x 22.9 mm, 26 parts (2 on the bottom side), 18 nets.
