dekuNukem/daytripper/pcb/misc/CC2541_Breakout_Board_Eagle_files/CC2541_Breakout_Board.brd

## EAGLE design pcb/misc/CC2541_Breakout_Board_Eagle_files/CC2541_Breakout_Board.brd (2018-10-05)

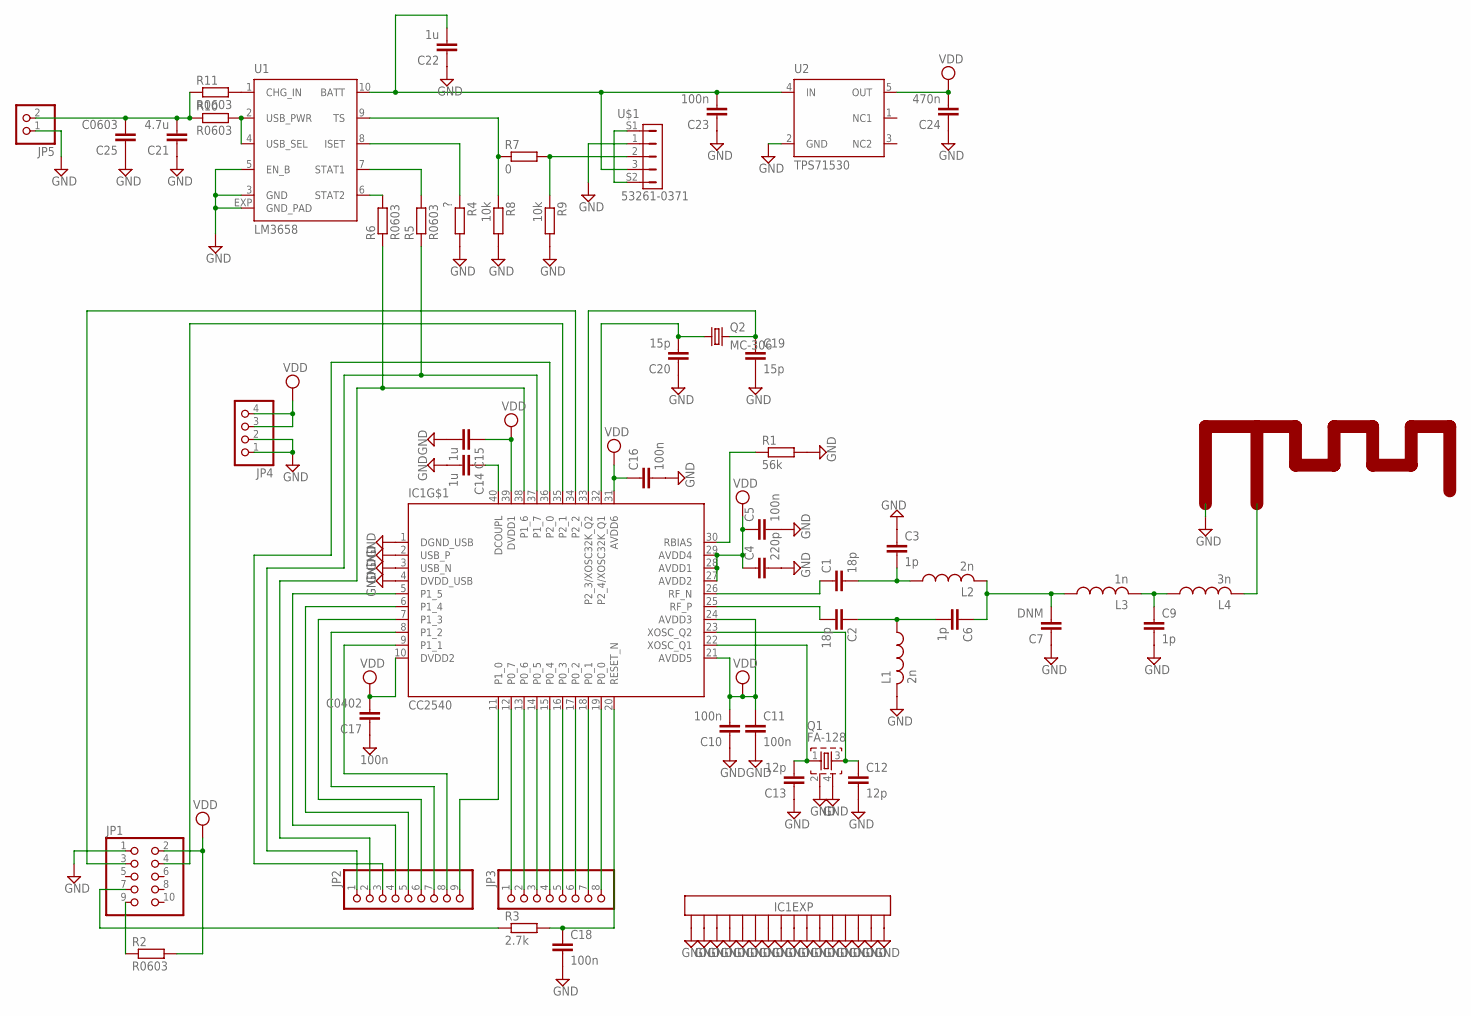
[picture p75: schematic CC2541_Breakout_Board.sch]

Parts:
A1: TI_2.4GHZ_MIFALEFT; TI_2.4GHZ_MIFA_LEFT
C1, C2: 18p; C0402
C3, C6, C9: 1p; C0402
C4: 220p; C0402
C5, C10, C11, C16, C18, C23: 100n; C0402
C7: DNM; C0402
C12, C13: 12p; C0402
C14, C15, C22: 1u; C0402
C17: C0402
C19, C20: 15p; C0402
C21: 4.7u; C0402
C24: 470n; C0402
C25: C0603
IC1: CC2540; QFN40-6X6
JP1: PINHD-2X51.27_SMD; 2X05_1.27_SMD
JP2: PINHD-1X9; 1X09
JP3: PINHD-1X8; 1X08
JP4: PINHD-1X4; 1X04
JP5: PINHD-1X2; 1X02
L1, L2: 2n; C0402
L3: 1n; C0402
L4: 3n; C0402
Q1: FA-128
Q2: MC-306
R1: 56k; C0402
R2, R5, R6, R10, R11: R0603; C0603
R3: 2.7k; C0402
R4: ?; C0402
R7: 0; C0402
R8, R9: 10k; C0402
U1: LM3658; LLP10
U2: TPS71530; SC70
U$1: 53261-0371; 53261-03

Connections:
CONNECTOR_MOUNT: U$1.S1, U$1.S2
GND: A1.GND, C3.1, C4.2, C5.2, C7.1, C9.2, C10.1, C11.2, C12.2, C13.1, C14.2, C15.2, C16.2, C17.1, C18.2, C19.2, C20.1, C21.1, C22.1, C23.1, C24.1, C25.1, IC1.1 (DGND_USB), IC1.2 (USB_P), IC1.3 (USB_N), IC1.4 (DVDD_USB), IC1.EXP@1 (EXP16), IC1.EXP@2 (EXP16), IC1.EXP@3 (EXP16), IC1.EXP@4 (EXP16), IC1.EXP@5 (EXP16), IC1.EXP@6 (EXP16), IC1.EXP@7 (EXP16), IC1.EXP@8 (EXP16), IC1.EXP@9 (EXP16), IC1.EXP@10 (EXP16), IC1.EXP@11 (EXP16), IC1.EXP@12 (EXP16), IC1.EXP@13 (EXP16), IC1.EXP@14 (EXP16), IC1.EXP@15 (EXP16), IC1.EXP@16 (EXP16), JP1.1, JP4.1, JP4.2, JP5.1, L1.2, Q1.2, Q1.4, R1.2, R4.2, R8.2, R9.2, U1.3 (GND), U1.5 (EN_B), U1.EXP (GND_PAD), U2.2 (GND), U$1.1
unnamed: C1.1, IC1.26 (RF_N)
unnamed: C2.2, IC1.25 (RF_P)
unnamed: C1.2, C3.2, L2.1
unnamed: C2.1, C6.2, L1.1
unnamed: C6.1, C7.2, L2.2, L3.1
unnamed: C9.1, L3.2, L4.1
unnamed: IC1.30 (RBIAS), R1.1
unnamed: C13.2, IC1.22 (XOSC_Q1), Q1.1
unnamed: C12.1, IC1.23 (XOSC_Q2), Q1.3
unnamed: C14.1, IC1.40 (DCOUPL)
unnamed: JP1.7, R3.1
unnamed: JP1.9, R2.1
unnamed: IC1.34 (P2_2), JP1.3
unnamed: IC1.35 (P2_1), JP1.4
unnamed: C18.1, IC1.20 (RESET_N), R3.2
unnamed: C20.2, IC1.32 (P2_4/XOSC32K_Q1), Q2.1
unnamed: C19.1, IC1.33 (P2_3/XOSC32K_Q2), Q2.4 (2)
unnamed: IC1.19 (P0_0), JP3.8
unnamed: IC1.18 (P0_1), JP3.7
unnamed: IC1.17 (P0_2), JP3.6
unnamed: IC1.16 (P0_3), JP3.5
unnamed: IC1.15 (P0_4), JP3.4
unnamed: IC1.14 (P0_5), JP3.3
unnamed: IC1.13 (P0_6), JP3.2
unnamed: IC1.12 (P0_7), JP3.1
unnamed: IC1.11 (P1_0), JP2.9
unnamed: IC1.9 (P1_1), JP2.8
unnamed: IC1.7 (P1_3), JP2.6
unnamed: IC1.8 (P1_2), JP2.7
unnamed: R10.2, U1.2 (USB_PWR), U1.4 (USB_SEL)
unnamed: IC1.6 (P1_4), JP2.5
unnamed: IC1.38 (P1_6), JP2.2, R6.1
unnamed: IC1.37 (P1_7), JP2.1, R5.1
unnamed: R4.1, U1.8 (ISET)
unnamed: C21.2, C25.2, JP5.2, R10.1, R11.1
unnamed: C22.2, C23.2, U1.10 (BATT), U2.4 (IN), U$1.3
unnamed: R5.2, U1.7 (STAT1)
unnamed: R6.2, U1.6 (STAT2)
unnamed: IC1.36 (P2_0), JP2.3
unnamed: R7.2, R9.1, U$1.2
unnamed: R7.1, R8.1, U1.9 (TS)
unnamed: IC1.5 (P1_5), JP2.4
unnamed: R11.2, U1.1 (CHG_IN)
unnamed: A1.FEED, L4.2
NC2: U2.3 (NC2)
VDD: C4.1, C5.1, C10.2, C11.1, C15.1, C16.1, C17.2, C24.2, IC1.10 (DVDD2), IC1.21 (AVDD5), IC1.24 (AVDD3), IC1.27 (AVDD2), IC1.28 (AVDD1), IC1.29 (AVDD4), IC1.31 (AVDD6), IC1.39 (DVDD1), JP1.2, JP4.3, JP4.4, R2.2, U2.5 (OUT)

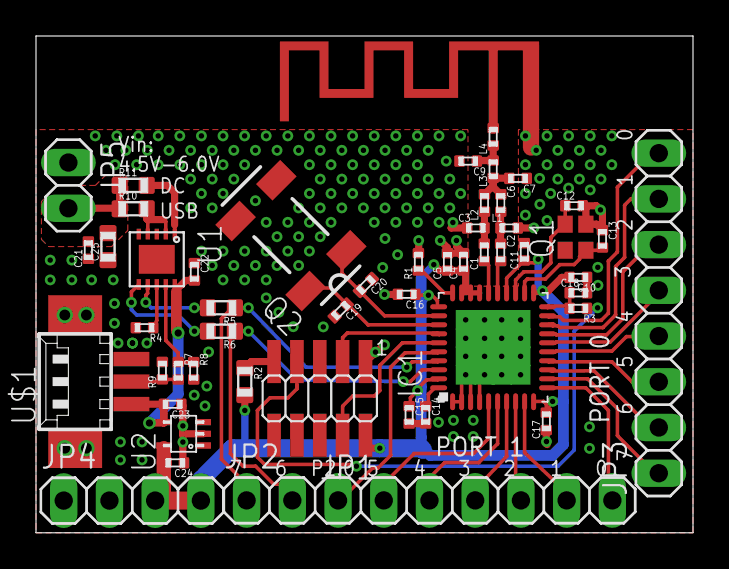
[picture p76: board CC2541_Breakout_Board.brd from above]

Board: 2 copper layers, 36.5 x 27.6 mm, 51 parts (0 on the bottom side), 47 nets.
