dekuNukem/daytripper/pcb/misc/sparkfun-nrf52832-breakout-EAGLE/sparkfun-nrf52832-breakout.brd

## EAGLE design pcb/misc/sparkfun-nrf52832-breakout-EAGLE/sparkfun-nrf52832-breakout.brd (2018-10-05)

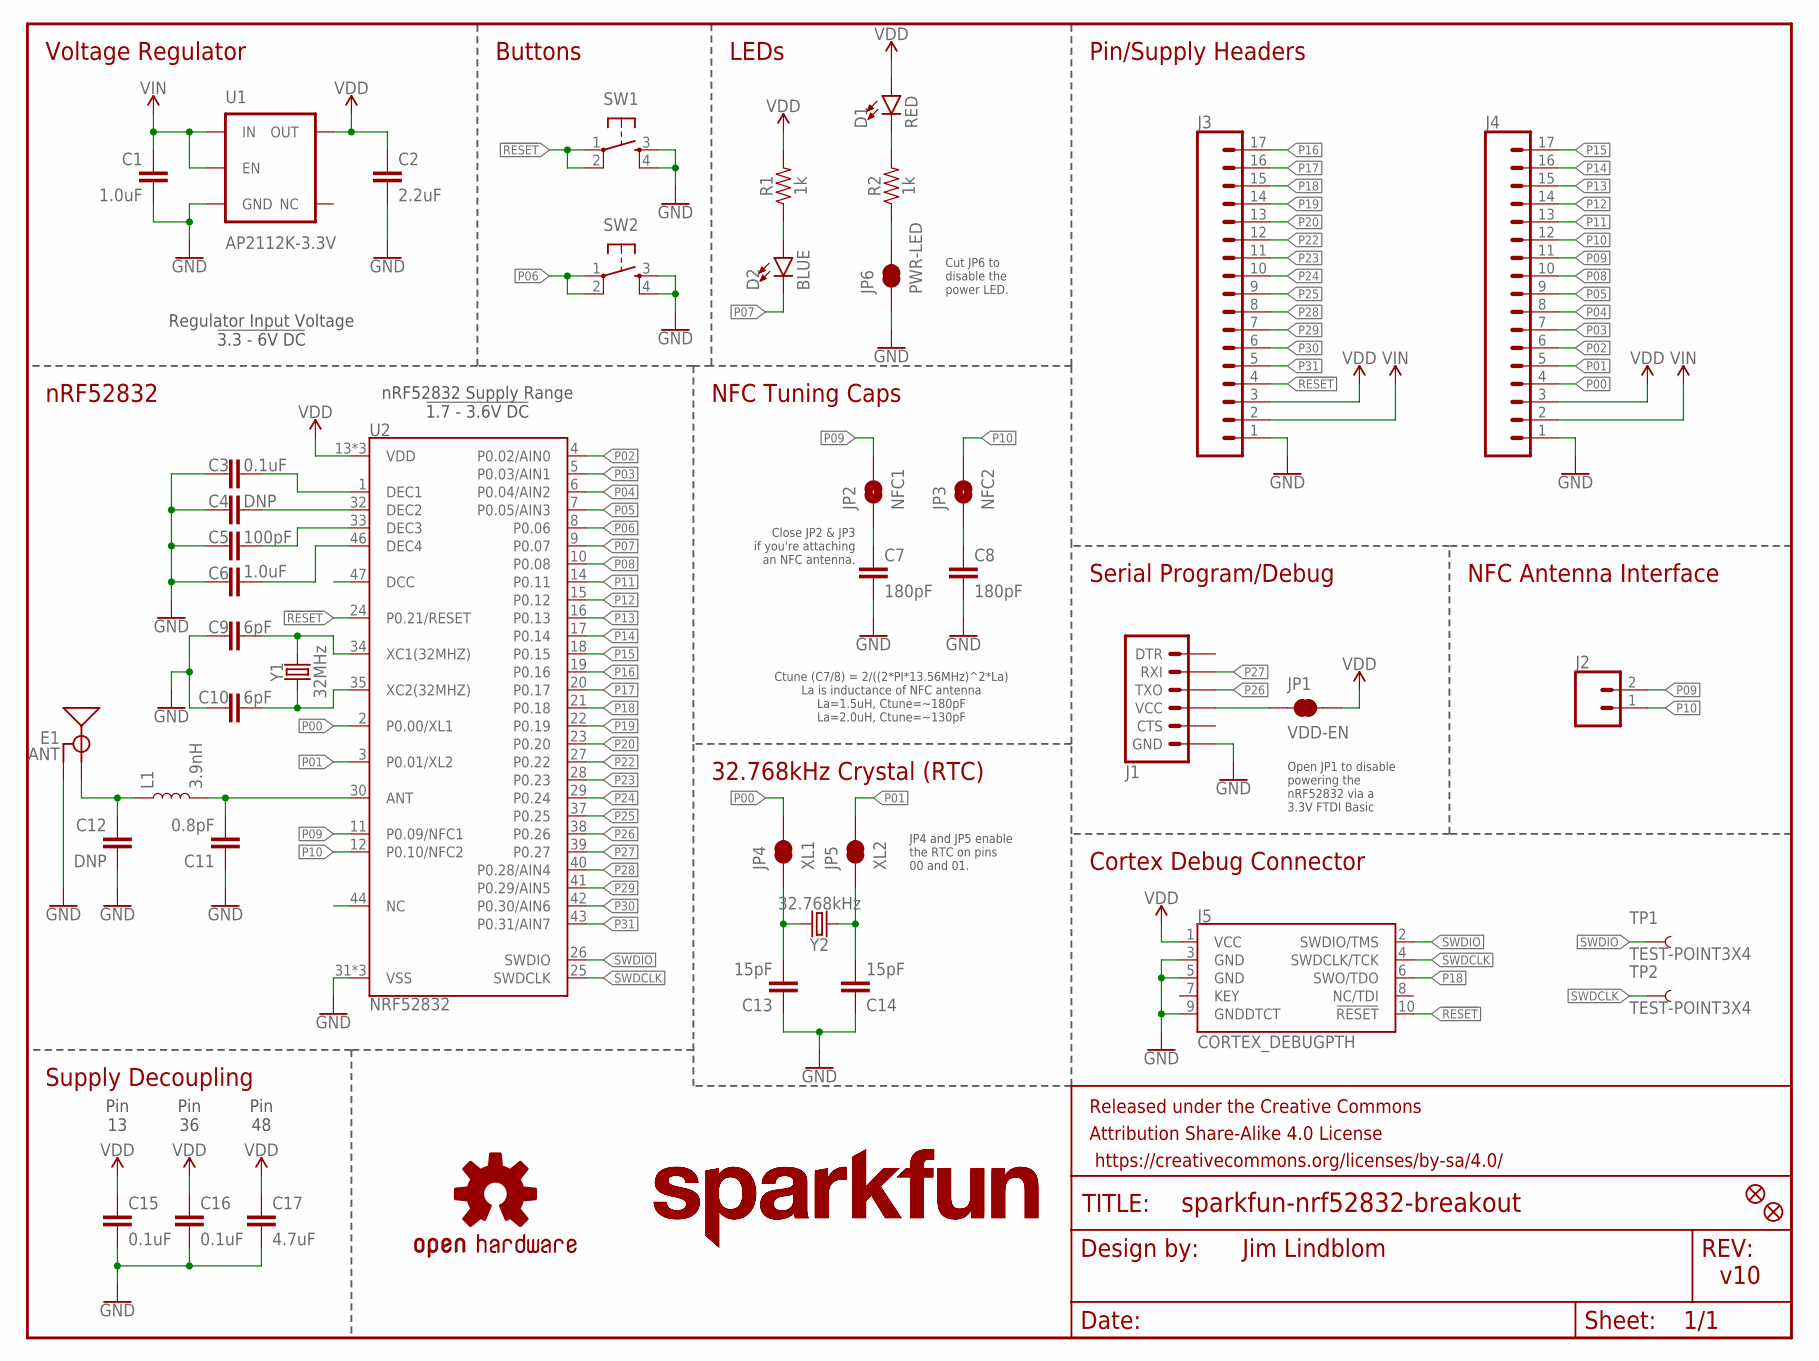
[picture p77: schematic sparkfun-nrf52832-breakout.sch]

Parts:
C1: 1.0uF; 0603
C2: 2.2uF; 0603
C3, C15, C16: 0.1uF; 0402
C4, C12: DNP; 0402
C5: 100pF; 0402
C6: 1.0uF; 0402
C7, C8: 180pF; 0603
C9, C10: 6pF; 0402
C11: 0.8pF; 0402
C13, C14: 15pF; 0402
C17: 4.7uF; 0603
D1: RED; LED-0603
D2: BLUE; LED-0603
E1: ANT; TRACE_ANTENNA_2.4GHZ_15.2MM
FD1, FD2: FIDUCIALUFIDUCIAL; FIDUCIAL-MICRO
FRAME1: FRAME-LETTER; CREATIVE_COMMONS
J1: ARDUINO_SERIAL_PROGRAMPTH; 1X06
J2: CONN_02PTH; 1X02
J3, J4: CONN_17; 1X17
J5: CORTEX_DEBUGPTH; 2X5-PTH-1.27MM
JP1: VDD-EN; SMT-JUMPER_2_NC_TRACE_SILK
JP2: NFC1; SMT-JUMPER_2_NO_SILK
JP3: NFC2; SMT-JUMPER_2_NO_SILK
JP4: XL1; PAD-JUMPER-2-NC_BY_TRACE_YES_SILK
JP5: XL2; PAD-JUMPER-2-NC_BY_TRACE_YES_SILK
JP6: PWR-LED; PAD-JUMPER-2-NC_BY_TRACE_YES_SILK
L1: 3.9nH; 0402
LOGO1: OSHW-LOGOMINI; OSHW-LOGO-MINI
LOGO2, LOGO3: SFE_LOGO_NAME.1_INCH; SFE_LOGO_NAME_.1
R1, R2: 1k; 0603
SW1, SW2: SWITCH_SPST_4_PINRECT; TACTILE_SWITCH_SMD_4.6X2.8MM
TP1, TP2: TEST-POINT3X4; PAD.03X.04
U1: AP2112K-3.3V; SOT23-5
U2: NRF52832; QFN48-6X6MM
Y1: 32MHz; CRYSTAL-SMD-2.0X1.6MM
Y2: 32.768kHz; CRYSTAL-SMD-3.2X1.5MM

Connections:
!RESET!: J3.4, J5.10 (!RESET), SW1.1, SW1.2, U2.24 (P0.21/RESET)
ANT: C11.2, L1.2, U2.30 (ANT)
DCC: U2.47 (DCC)
DEC1: C3.2, U2.1 (DEC1)
DEC2: C4.2, U2.32 (DEC2)
DEC3: C5.2, U2.33 (DEC3)
DEC4: C6.2, U2.46 (DEC4)
GND: C1.2, C2.2, C3.1, C4.1, C5.1, C6.1, C7.2, C8.2, C9.1, C10.2, C11.1, C12.2, C13.1, C14.1, C15.2, C16.2, C17.2, E1.GND, J1.6 (GND), J3.1, J4.1, J5.3 (GND), J5.5 (GND), J5.9 (GNDDTCT), JP6.1, SW1.3, SW1.4, SW2.3, SW2.4, U1.2 (GND), U2.31 (VSS), U2.45 (VSS), U2.EP (VSS)
unnamed: JP6.2, R2.1
unnamed: C13.2, JP4.1, Y2.P$2 (2)
unnamed: C14.2, JP5.1, Y2.P$1 (1)
unnamed: C12.1, E1.ANT (SIGNAL), L1.1
unnamed: D1.C, R2.2
unnamed: J1.4 (VCC), JP1.1
unnamed: D2.A, R1.1
NC: U2.44 (NC)
NFC1: C7.1, JP2.1
NFC2: C8.1, JP3.1
P00: J4.4, JP4.2, U2.2 (P0.00/XL1)
P01: J4.5, JP5.2, U2.3 (P0.01/XL2)
P02: J4.6, U2.4 (P0.02/AIN0)
P03: J4.7, U2.5 (P0.03/AIN1)
P04: J4.8, U2.6 (P0.04/AIN2)
P05: J4.9, U2.7 (P0.05/AIN3)
P06: SW2.1, SW2.2, U2.8 (P0.06)
P07: D2.C, U2.9 (P0.07)
P08: J4.10, U2.10 (P0.08)
P09: J2.2, J4.11, JP2.2, U2.11 (P0.09/NFC1)
P10: J2.1, J4.12, JP3.2, U2.12 (P0.10/NFC2)
P11: J4.13, U2.14 (P0.11)
P12: J4.14, U2.15 (P0.12)
P13: J4.15, U2.16 (P0.13)
P14: J4.16, U2.17 (P0.14)
P15: J4.17, U2.18 (P0.15)
P16: J3.17, U2.19 (P0.16)
P17: J3.16, U2.20 (P0.17)
P18: J3.15, J5.6 (SWO/TDO), U2.21 (P0.18)
P19: J3.14, U2.22 (P0.19)
P20: J3.13, U2.23 (P0.20)
P22: J3.12, U2.27 (P0.22)
P23: J3.11, U2.28 (P0.23)
P24: J3.10, U2.29 (P0.24)
P25: J3.9, U2.37 (P0.25)
P26: J1.3 (TXO), U2.38 (P0.26)
P27: J1.2 (RXI), U2.39 (P0.27)
P28: J3.8, U2.40 (P0.28/AIN4)
P29: J3.7, U2.41 (P0.29/AIN5)
P30: J3.6, U2.42 (P0.30/AIN6)
P31: J3.5, U2.43 (P0.31/AIN7)
SWDCLK: J5.4 (SWDCLK/TCK), TP2.P$1, U2.25 (SWDCLK)
SWDIO: J5.2 (SWDIO/TMS), TP1.P$1, U2.26 (SWDIO)
VDD: C2.1, C15.1, C16.1, C17.1, D1.A, J3.3, J4.3, J5.1 (VCC), JP1.2, R1.2, U1.5 (OUT), U2.13 (VDD), U2.36 (VDD), U2.48 (VDD)
VIN: C1.1, J3.2, J4.2, U1.1 (IN), U1.3 (EN)
XC1: C9.2, U2.34 (XC1(32MHZ)), Y1.3 (2)
XC2: C10.1, U2.35 (XC2(32MHZ)), Y1.1

Notes on the sheet:
Pin 13
Pin 36
Pin 48
v10
Jim Lindblom
Ctune (C7/8) = 2/((2*PI*13.56MHz)^2*La) La is inductance of NFC antenna La=1.5uH, Ctune=~180pF La=2.0uH, Ctune=~130pF
Voltage Regulator
Buttons
LEDs
Pin/Supply Headers
nRF52832
32.768kHz Crystal (RTC)
Supply Decoupling
NFC Tuning Caps
Cortex Debug Connector
Serial Program/Debug
NFC Antenna Interface
Open JP1 to disable powering the nRF52832 via a 3.3V FTDI Basic
Close JP2 & JP3 if you're attaching an NFC antenna.
JP4 and JP5 enable the RTC on pins 00 and 01.
Regulator Input Voltage !3.3 - 6V DC!
nRF52832 Supply Range !1.7 - 3.6V DC!
Cut JP6 to disable the power LED.

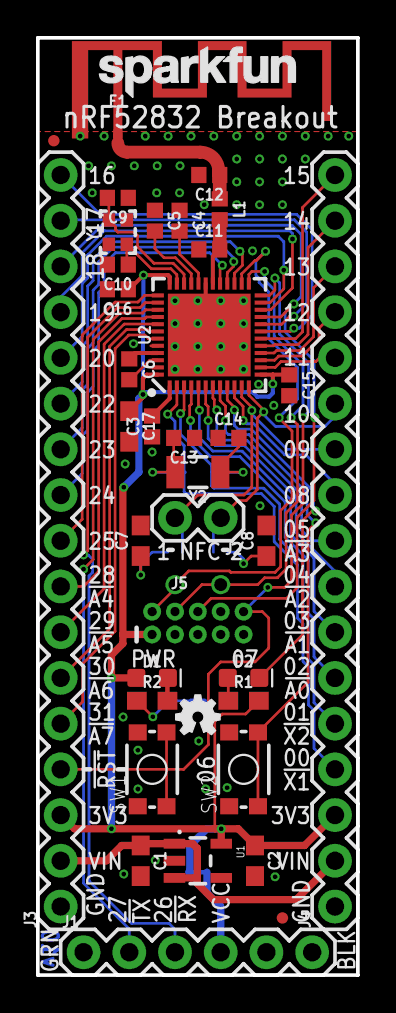
[picture p78: board sparkfun-nrf52832-breakout.brd from above]

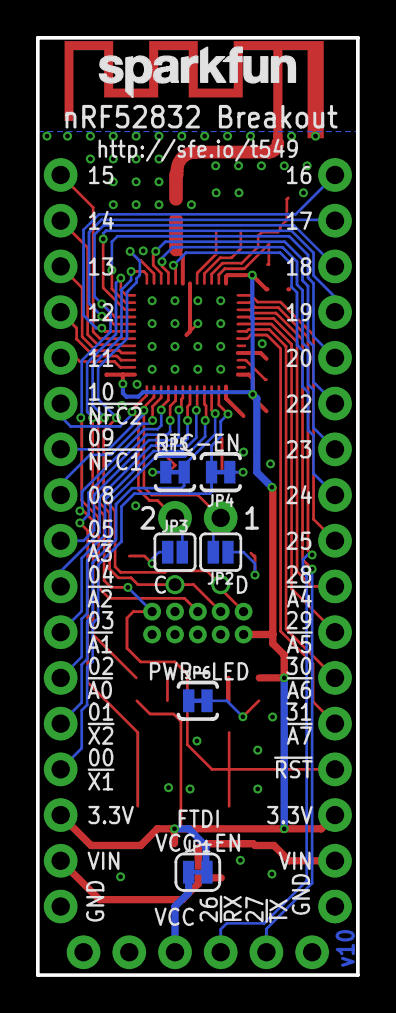
[picture p79: board sparkfun-nrf52832-breakout.brd from below]

Board: 2 copper layers, 17.8 x 52.1 mm, 48 parts (9 on the bottom side), 53 nets.
