dekuNukem/daytripper/pcb/misc/esp32-thing-v10/esp32-thing.brd

## EAGLE design pcb/misc/esp32-thing-v10/esp32-thing.brd (2018-10-05)

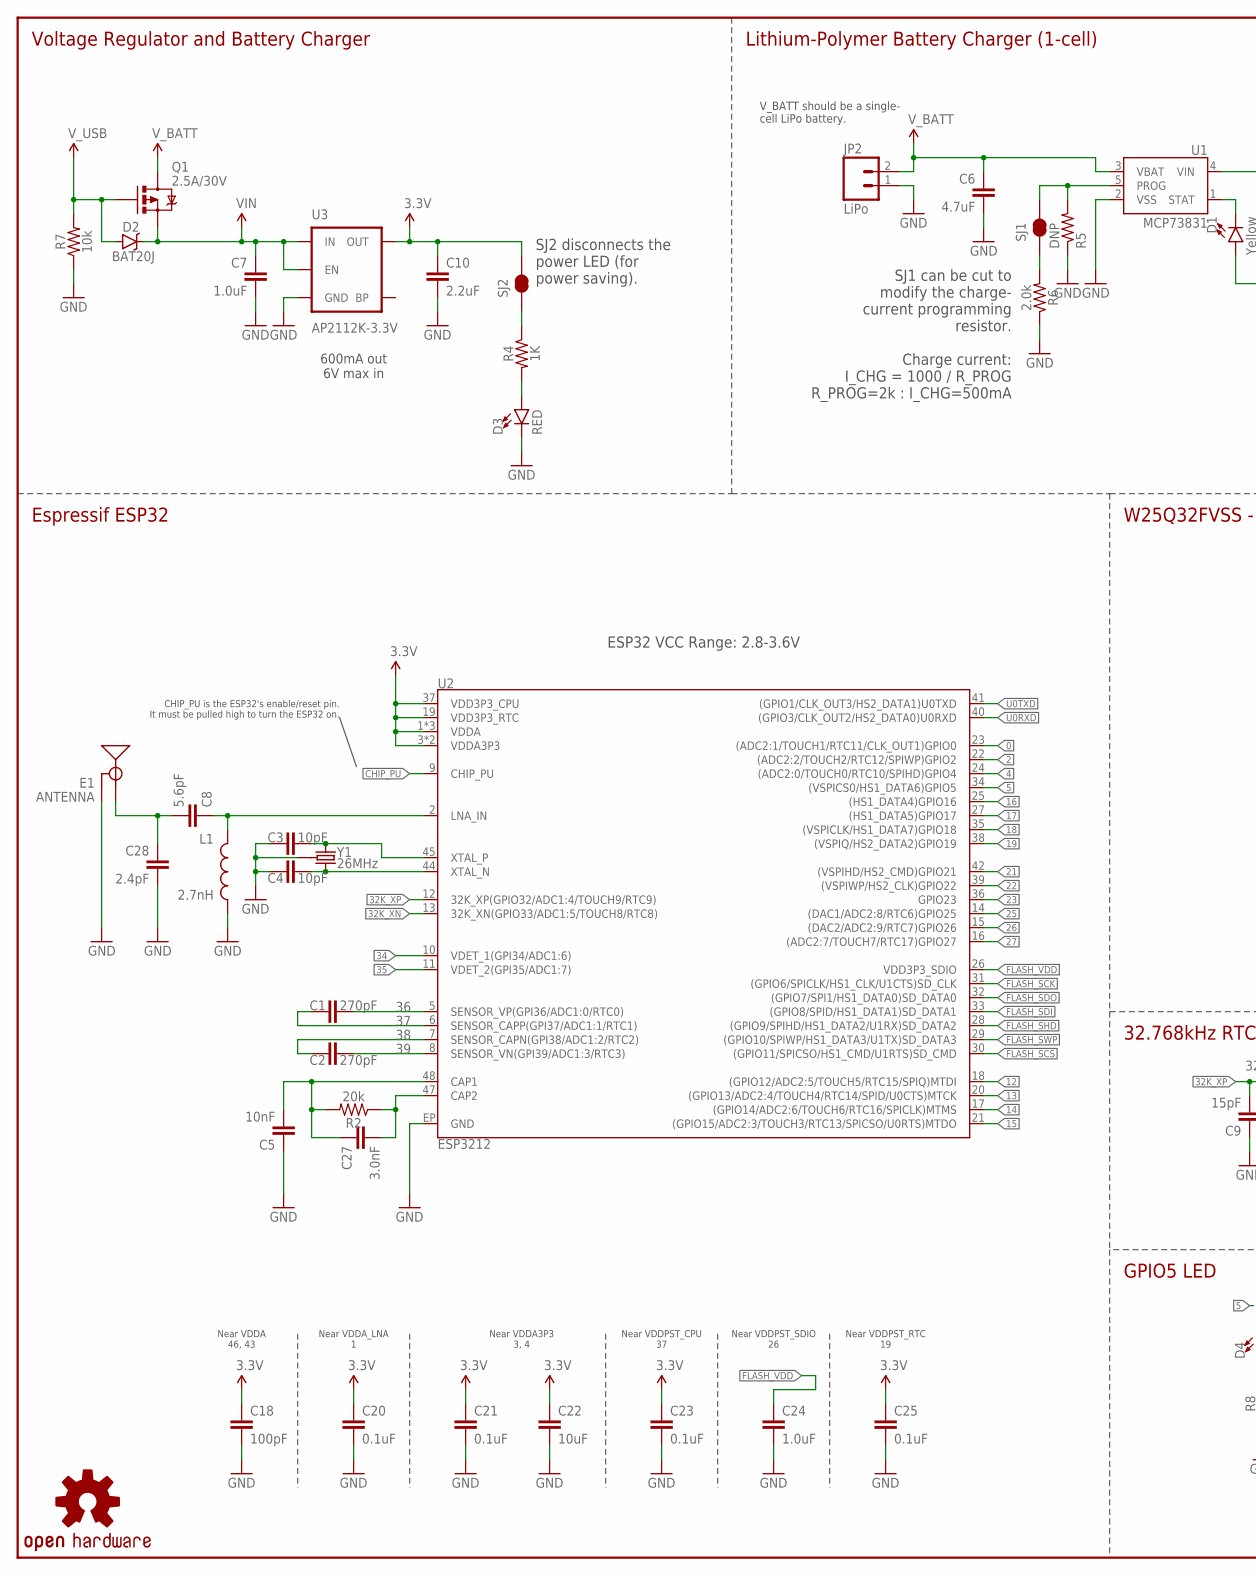
[picture p80: schematic esp32-thing.sch, part in row 1, column 1]

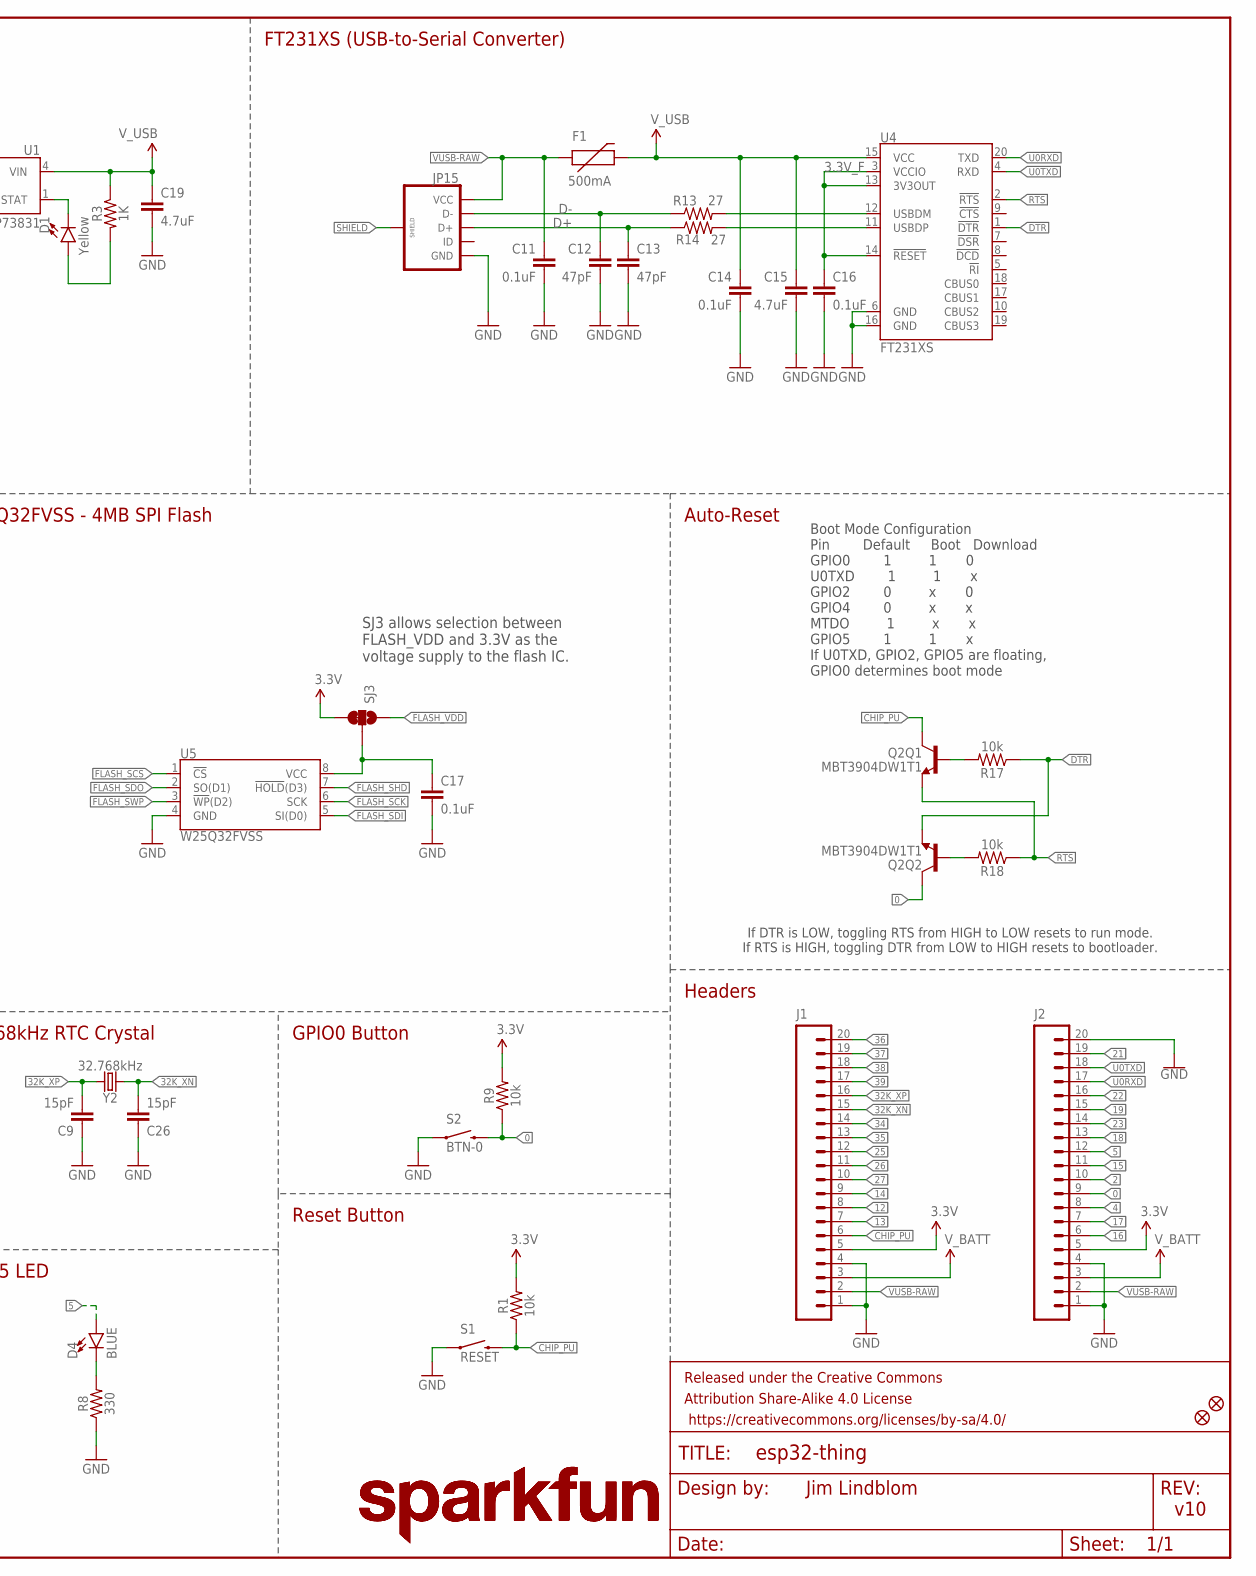
[picture p81: schematic esp32-thing.sch, part in row 1, column 2]

Parts:
C1, C2: 270pF; 0603
C3, C4: 10pF; 0603
C5: 10nF; 0603
C6, C19: 4.7uF; 0603
C7: 1.0uF; 0805
C8: 5.6pF; 0603
C9, C26: 15pF; 0603
C10: 2.2uF; 0603
C11, C14, C16, C17, C20, C21, C23, C25: 0.1uF; 0603
C12, C13: 47pF; 0603
C15: 4.7uF; 0603-CAP
C18: 100pF; 0603
C22: 10uF; 0603
C24: 1.0uF; 0603
C27: 3.0nF; 0603
C28: 2.4pF; 0603
D1: Yellow; LED-0603
D2: BAT20J; SOD-323
D3: RED; LED-0603
D4: BLUE; LED-0603
E1: ANTENNA; TRACE_ANTENNA_2.4GHZ_25.7MM_TUNED
F1: 500mA; PTC-1206
FD1, FD2: FIDUCIALUFIDUCIAL; MICRO-FIDUCIAL
FRAME1: FRAME-LEDGER; CREATIVE_COMMONS
J1, J2: M20NOSILK; 1X20_NOSILK
JP2: LiPo; JST-2-PTH
JP15: USB_MICROB_PLUGCONN-11752; USB-B-MICRO-SMD_V03
L1: 2.7nH; 0603
LOGO1, LOGO3: SFE_LOGO_NAME.2_INCH; SFE_LOGO_NAME_.2
LOGO2: OSHW-LOGOMINI; OSHW-LOGO-MINI
Q1: 2.5A/30V; SOT23-3
Q2: MBT3904DW1T1; SC70-6
R1, R7, R9, R17, R18: 10k; 0603
R2: 20k; 0603
R3, R4: 1K; 0603
R5: DNP; 1/6W-RES
R6: 2.0k; 0603
R8: 330; 0603
R13, R14: 27; 0603
S1: RESET; TACTILE_SWITCH_SMD_4.6X2.8MM
S2: BTN-0; TACTILE_SWITCH_SMD_4.6X2.8MM
SJ1, SJ2: JUMPER-PAD-2-NC_BY_TRACE; PAD-JUMPER-2-NC_BY_TRACE_YES_SILK
SJ3: JUMPER-PAD-3-2OF3_NC_BY_TRACE_SMALL; PAD-JUMPER-3-2OF3_NC_BY_TRACE_YES_SILK_FULL_BOX
U1: MCP73831; SOT23-5
U2: ESP3212; QFN48-0.4MM
U3: AP2112K-3.3V; SOT23-5
U4: FT231XS; SSOP20_L
U5: W25Q32FVSS; SOIC-8
Y1: 26MHz; CRYSTAL-SMD-3.2X2.5
Y2: 32.768kHz; CRYSTAL-SMD-3.2X1.5MM

Connections:
0: J2.9, Q2.6 (C), R9.1, S2.3 (2), S2.4 (2), U2.23 ((ADC2:1/TOUCH1/RTC11/CLK_OUT1)GPIO0)
2: J2.10, U2.22 ((ADC2:2/TOUCH2/RTC12/SPIWP)GPIO2)
3.3V: C10.1, C18.1, C20.1, C21.1, C22.1, C23.1, C25.1, J1.5, J2.5, R1.2, R9.2, SJ2.2, SJ3.3, U2.1 (VDDA), U2.3 (VDDA3P3), U2.4 (VDDA3P3), U2.19 (VDD3P3_RTC), U2.37 (VDD3P3_CPU), U2.43 (VDDA), U2.46 (VDDA), U3.5 (OUT)
3.3V_F: C16.1, U4.3 (VCCIO), U4.13 (3V3OUT), U4.14 (!RESET)
4: J2.8, U2.24 ((ADC2:0/TOUCH0/RTC10/SPIHD)GPIO4)
5: D4.A, J2.12, U2.34 ((VSPICS0/HS1_DATA6)GPIO5)
12: J1.8, U2.18 ((GPIO12/ADC2:5/TOUCH5/RTC15/SPIQ)MTDI)
13: J1.7, U2.20 ((GPIO13/ADC2:4/TOUCH4/RTC14/SPID/U0CTS)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)
14: J1.9, U2.17 ((GPIO14/ADC2:6/TOUCH6/RTC16/SPICLK)MTMS)
15: J2.11, U2.21 ((GPIO15/ADC2:3/TOUCH3/RTC13/SPICSO/U0RT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)
16: J2.6, U2.25 ((HS1_DATA4)GPIO16)
17: J2.7, U2.27 ((HS1_DATA5)GPIO17)
18: J2.13, U2.35 ((VSPICLK/HS1_DATA7)GPIO18)
19: J2.15, U2.38 ((VSPIQ/HS2_DATA2)GPIO19)
21: J2.19, U2.42 ((VSPIHD/HS2_CMD)GPIO21)
22: J2.16, U2.39 ((VSPIWP/HS2_CLK)GPIO22)
23: J2.14, U2.36 (GPIO23)
25: J1.12, U2.14 ((DAC1/ADC2:8/RTC6)GPIO25)
26: J1.11, U2.15 ((DAC2/ADC2:9/RTC7)GPIO26)
27: J1.10, U2.16 ((ADC2:7/TOUCH7/RTC17)GPIO27)
32K_XN: C26.2, J1.15, U2.13 (32K_XN(GPIO33/ADC1:5/TOUCH8/RTC8)), Y2.P$2 (2)
32K_XP: C9.2, J1.16, U2.12 (32K_XP(GPIO32/ADC1:4/TOUCH9/RTC9)), Y2.P$1 (1)
34: J1.14, U2.10 (VDET_1(GPI34/ADC1:6))
35: J1.13, U2.11 (VDET_2(GPI35/ADC1:7))
36: C1.2, J1.20, U2.5 (SENSOR_VP(GPI36/ADC1:0/RTC0))
37: C1.1, J1.19, U2.6 (SENSOR_CAPP(GPI37/ADC1:1/RTC1))
38: C2.1, J1.18, U2.7 (SENSOR_CAPN(GPI38/ADC1:2/RTC2))
39: C2.2, J1.17, U2.8 (SENSOR_VN(GPI39/ADC1:3/RTC3))
CAP_10N: C5.2, C27.1, R2.2, U2.48 (CAP1)
CHIP_PU: J1.6, Q2.3 (C), R1.1, S1.3 (2), S1.4 (2), U2.9 (CHIP_PU)
D+: C13.1, JP15.D+, R14.1
D-: C12.1, JP15.D-, R13.1
DTR: Q2.1 (E), R17.1, U4.1 (!DTR)
FLASH_SCK: U2.31 ((GPIO6/SPICLK/HS1_CLK/U1CTS)SD_CLK), U5.6 (SCK)
FLASH_SCS: U2.30 ((GPIO11/SPICSO/HS1_CMD/U1RTS)SD_CMD), U5.1 (!CS!)
FLASH_SDI: U2.33 ((GPIO8/SPID/HS1_DATA1)SD_DATA1), U5.5 (SI(D0))
FLASH_SDO: U2.32 ((GPIO7/SPI1/HS1_DATA0)SD_DATA0), U5.2 (SO(D1))
FLASH_SHD: U2.28 ((GPIO9/SPIHD/HS1_DATA2/U1RX)SD_DATA2), U5.7 (!HOLD!(D3))
FLASH_SWP: U2.29 ((GPIO10/SPIWP/HS1_DATA3/U1TX)SD_DATA3), U5.3 (!WP!(D2))
FLASH_VDD: C24.1, SJ3.1, U2.26 (VDD3P3_SDIO)
GND: C3.1, C4.1, C5.1, C6.2, C7.2, C9.1, C10.2, C11.2, C12.2, C13.2, C14.2, C15.2, C16.2, C17.2, C18.2, C19.2, C20.2, C21.2, C22.2, C23.2, C24.2, C25.2, C26.1, C28.2, D3.C, E1.GND, E1.GND2 (GND), J1.1, J1.4, J2.1, J2.4, J2.20, JP2.1, JP15.GND, L1.2, R5.1, R6.1, R7.1, R8.1, S1.1, S1.2 (1), S2.1, S2.2 (1), U1.2 (VSS), U2.EP (GND), U3.2 (GND), U4.6 (GND), U4.16 (GND), U5.4 (GND), Y1.2 (GND), Y1.4 (GND)
LNA_IN: C8.1, L1.1, U2.2 (LNA_IN)
unnamed: D4.C, R8.2
unnamed: D3.A, R4.2
unnamed: R4.1, SJ2.1
unnamed: C27.2, R2.1, U2.47 (CAP2)
unnamed: R13.2, U4.12 (USBDM)
unnamed: R14.2, U4.11 (USBDP)
unnamed: D1.C, U1.1 (STAT)
unnamed: Q2.5 (B), R17.2
unnamed: C17.1, SJ3.2, U5.8 (VCC)
unnamed: Q2.2 (B), R18.2
unnamed: C3.2, U2.45 (XTAL_P), Y1.1
unnamed: R5.2, SJ1.2, U1.5 (PROG)
unnamed: C4.2, U2.44 (XTAL_N), Y1.3 (2)
unnamed: R6.2, SJ1.1
unnamed: D1.A, R3.2
RTS: Q2.4 (E), R18.1, U4.2 (!RTS)
SHIELD: JP15.SHIELD1 (SHIELD), JP15.SHIELD2 (SHIELD), JP15.SHIELD3 (SHIELD)
TRACE_ANT: C8.2, C28.1, E1.ANT (SIGNAL)
U0RXD: J2.17, U2.40 ((GPIO3/CLK_OUT2/HS2_DATA0)U0RXD), U4.20 (TXD)
U0TXD: J2.18, U2.41 ((GPIO1/CLK_OUT3/HS2_DATA1)U0TXD), U4.4 (RXD)
VIN: C7.1, D2.C, Q1.2 (S), U3.1 (IN), U3.3 (EN)
VUSB-RAW: C11.1, F1.1, J1.2, J2.2, JP15.VBUS (VCC)
V_BATT: C6.1, J1.3, J2.3, JP2.2, Q1.3 (D), U1.3 (VBAT)
V_USB: C14.1, C15.1, C19.1, D2.A, F1.2, Q1.1 (G), R3.1, R7.2, U1.4 (VIN), U4.15 (VCC)

Notes on the sheet:
Boot Mode Configuration Pin Default Boot Download GPIO0 1 1 0 U0TXD 1 1 x GPIO2 0 x 0 GPIO4 0 x x MTDO 1 x x GPIO5 1 1 x If U0TXD, GPIO2, GPIO5 are floating, GPIO0 determines boot mode
FT231XS (USB-to-Serial Converter)
V_BATT should be a single- cell LiPo battery.
Charge current: I_CHG = 1000 / R_PROG R_PROG=2k : I_CHG=500mA
Voltage Regulator and Battery Charger
SJ1 can be cut to modify the charge- current programming resistor.
Lithium-Polymer Battery Charger (1-cell)
600mA out 6V max in
Auto-Reset
Near VDDA 46, 43
Near VDDA_LNA 1
Near VDDA3P3 3, 4
Near VDDPST_CPU 37
Near VDDPST_SDIO 26
Near VDDPST_RTC 19
Espressif ESP32
W25Q32FVSS - 4MB SPI Flash
32.768kHz RTC Crystal
GPIO0 Button
Reset Button
GPIO5 LED
Headers
v10
Jim Lindblom
ESP32 VCC Range: 2.8-3.6V
SJ3 allows selection between FLASH_VDD and 3.3V as the voltage supply to the flash IC.
SJ2 disconnects the power LED (for power saving).
If DTR is LOW, toggling RTS from HIGH to LOW resets to run mode. If RTS is HIGH, toggling DTR from LOW to HIGH resets to bootloader.
CHIP_PU is the ESP32's enable/reset pin. It must be pulled high to turn the ESP32 on.

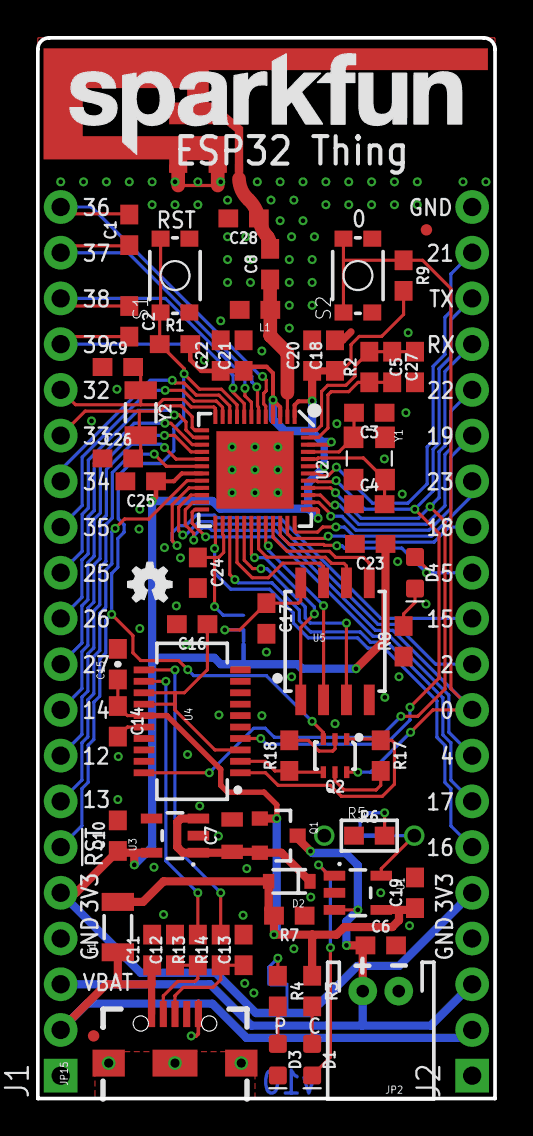
[picture p82: board esp32-thing.brd from above]

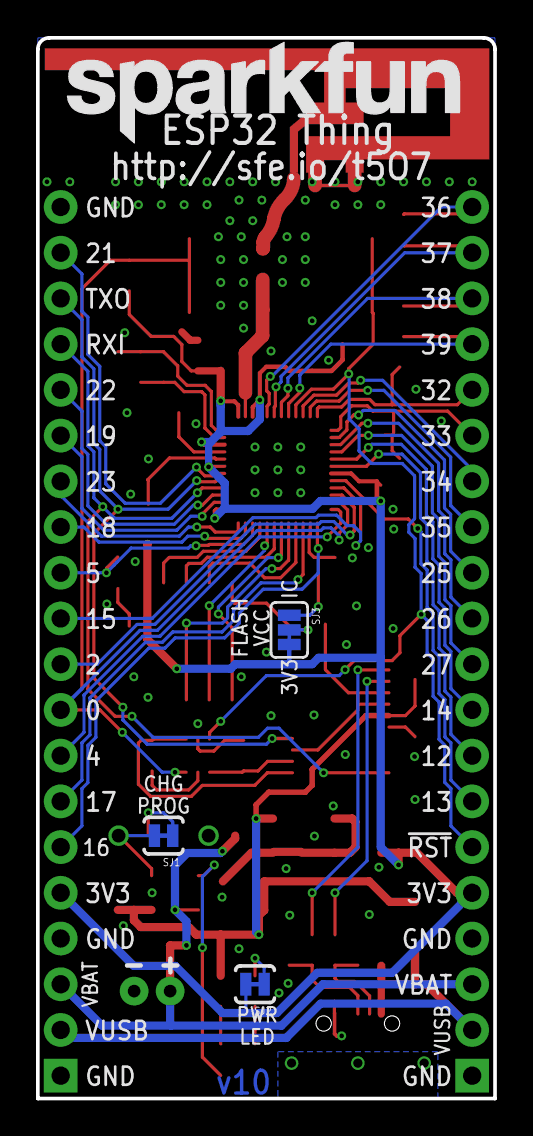
[picture p83: board esp32-thing.brd from below]

Board: 2 copper layers, 25.4 x 58.9 mm, 72 parts (4 on the bottom side), 66 nets.
