dekuNukem/daytripper/pcb/misc/Adafruit-VL53L0X-ToF-Distance-Sensor-PCB-master/Adafruit VL53L0X.brd

## EAGLE design pcb/misc/Adafruit-VL53L0X-ToF-Distance-Sensor-PCB-master/Adafruit VL53L0X.brd (2018-08-13)

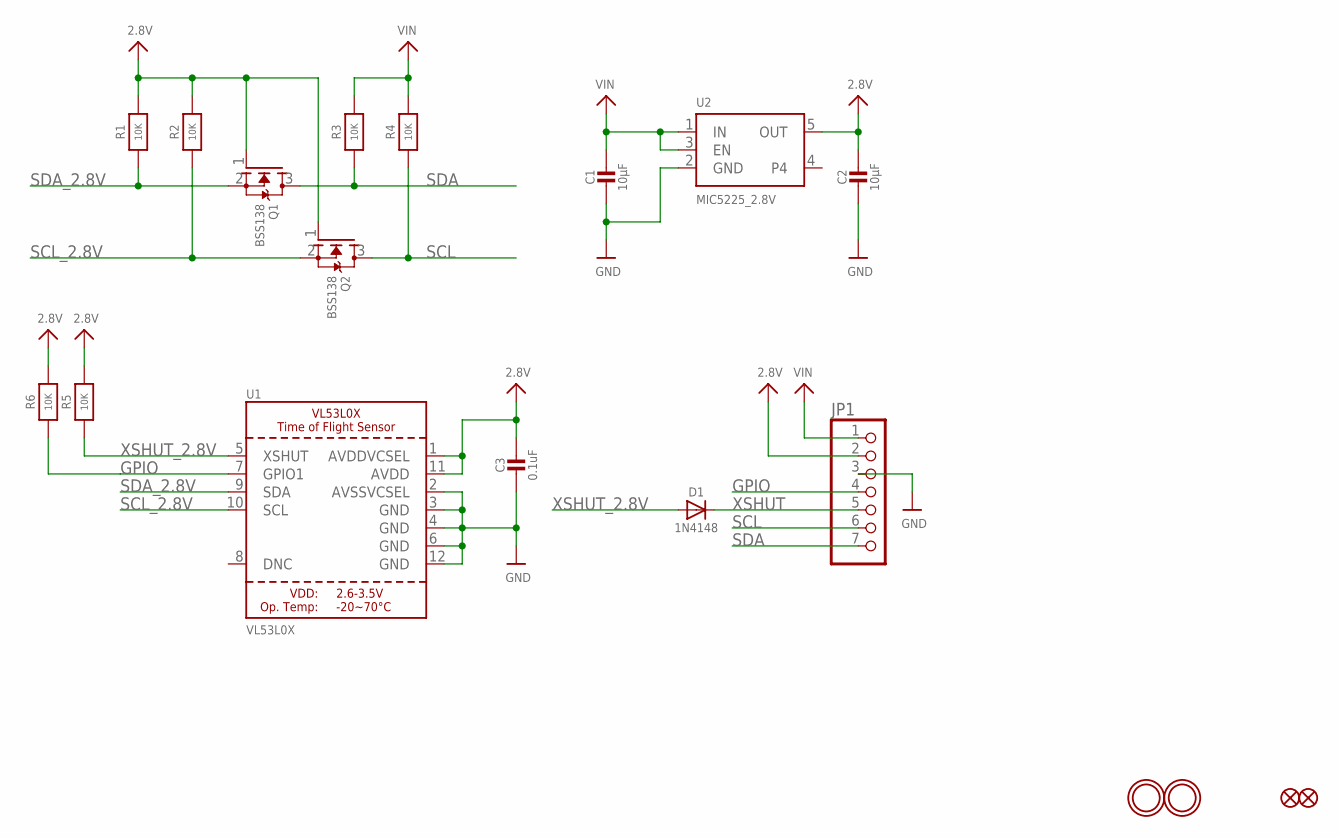
[picture p84: schematic Adafruit VL53L0X.sch]

Parts:
C1, C2: 10µF; 0805-NO
C3: 0.1uF; 0805-NO
D1: 1N4148; SOD-323
FID2, FID3: FIDUCIAL""; FIDUCIAL_1MM
JP1: HEADER-1X770MIL; 1X07_ROUND_70
Q1, Q2: BSS138; SOT23-WIDE
R1, R2, R3, R4, R5, R6: 10K; 0805-NO
U1: VL53L0X; LGA12_ST
U2: MIC5225_2.8V; SOT23-5
U$13, U$14: MOUNTINGHOLE2.5; MOUNTINGHOLE_2.5_PLATED

Connections:
2.8V: C2.1, C3.1, JP1.2, Q1.1 (G), Q2.1 (G), R1.2, R2.2, R5.2, R6.2, U1.1 (AVDDVCSEL), U1.11 (AVDD), U2.5 (OUT)
GND: C1.2, C2.2, C3.2, JP1.3, U1.2 (AVSSVCSEL), U1.3 (GND), U1.4 (GND), U1.6 (GND), U1.12 (GND), U2.2 (GND)
GPIO: JP1.4, R6.1, U1.7 (GPIO1)
SCL: JP1.6, Q2.3 (D), R4.1
SCL_2.8V: Q2.2 (S), R2.1, U1.10 (SCL)
SDA: JP1.7, Q1.3 (D), R3.1
SDA_2.8V: Q1.2 (S), R1.1, U1.9 (SDA)
VIN: C1.1, JP1.1, R3.2, R4.2, U2.1 (IN), U2.3 (EN)
XSHUT: D1.C, JP1.5
XSHUT_2.8V: D1.A, R5.1, U1.5 (XSHUT)

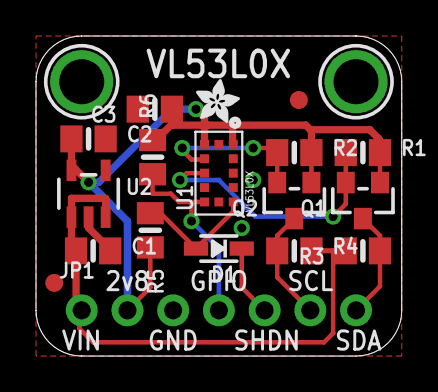
[picture p85: board Adafruit VL53L0X.brd from above]

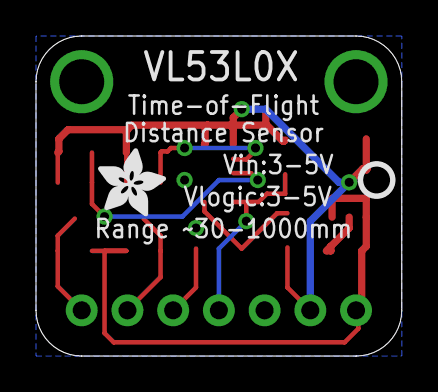
[picture p86: board Adafruit VL53L0X.brd from below]

Board: 2 copper layers, 20.3 x 17.8 mm, 22 parts (2 on the bottom side), 10 nets.

Other parts of the board:
U$12: PCBFEAT-REV-040
U$15: ADAFRUIT_3.5MM
U$18: ADAFRUIT_2.5MM
