dekuNukem/daytripper/firmware/code/tx/Src/ee.c

#include "ee.h"
#include "eeConfig.h"
#include <string.h>
#include "stm32f0xx_hal.h"

#define   PAGE                  0
#define   SECTOR                1

#if defined(STM32F103xB)
#define   _EE_SIZE              1024
#define   _EE_ADDR_INUSE        (((uint32_t)0x08000000) | (_EE_SIZE * _EE_USE_FLASH_PAGE_OR_SECTOR))
#define   _EE_FLASH_BANK        FLASH_BANK_1
#define   _EE_PAGE_OR_SECTOR    PAGE
#if (_EE_USE_FLASH_PAGE_OR_SECTOR > 127)
#error  "Please Enter currect address, maximum is (127)"
#endif
#endif

#if defined(STM32F103x8)
#define   _EE_MAX_SIZE          1024
#define   _EE_ADDR_INUSE        (((uint32_t)0x08000000) | (_EE_MAX_SIZE * _EE_USE_FLASH_PAGE_OR_SECTOR))
#define   _EE_FLASH_BANK        FLASH_BANK_1
#define   _EE_PAGE_OR_SECTOR    PAGE
#if (_EE_USE_FLASH_PAGE_OR_SECTOR > 63)
#error  "Please Enter currect address, maximum is (63)"
#endif
#endif

#if defined(STM32F103xC)
#define   _EE_SIZE              2048
#define   _EE_ADDR_INUSE        (((uint32_t)0x08000000) | (_EE_SIZE * _EE_USE_FLASH_PAGE_OR_SECTOR))
#define   _EE_FLASH_BANK        FLASH_BANK_1
#define   _EE_PAGE_OR_SECTOR    PAGE
#if (_EE_USE_FLASH_PAGE_OR_SECTOR > 127)
#error  "Please Enter currect address, maximum is (127)"
#endif
#endif

#if defined(STM32F103xD)
#define   _EE_SIZE              2048
#define   _EE_ADDR_INUSE        (((uint32_t)0x08000000) | (_EE_SIZE * _EE_USE_FLASH_PAGE_OR_SECTOR))
#define   _EE_FLASH_BANK        FLASH_BANK_1
#define   _EE_PAGE_OR_SECTOR    PAGE
#if (_EE_USE_FLASH_PAGE_OR_SECTOR > 191)
#error  "Please Enter currect address, maximum is (191)"
#endif
#endif

#if defined(STM32F103xE)
#define   _EE_SIZE              2048
#define   _EE_ADDR_INUSE        (((uint32_t)0x08000000) | (_EE_SIZE * _EE_USE_FLASH_PAGE_OR_SECTOR))
#define   _EE_FLASH_BANK        FLASH_BANK_1
#define   _EE_PAGE_OR_SECTOR    PAGE
#if (_EE_USE_FLASH_PAGE_OR_SECTOR > 255)
#error  "Please Enter currect address, maximum is (255)"
#endif
#endif

#if defined(STM32F030x4) || defined(STM32F042x4)  || defined(STM32F070x4)
#define   _EE_SIZE              1024
#define   _EE_ADDR_INUSE        (((uint32_t)0x08000000) | (_EE_SIZE * _EE_USE_FLASH_PAGE_OR_SECTOR))
#define   _EE_PAGE_OR_SECTOR    PAGE
#if (_EE_USE_FLASH_PAGE_OR_SECTOR > 15)
#error  "Please Enter currect address, maximum is (15)"
#endif
#endif

#if  defined(STM32F030x6) || defined(STM32F042x6) || defined(STM32F070x6)
#define   _EE_SIZE              1024
#define   _EE_ADDR_INUSE        (((uint32_t)0x08000000) | (_EE_SIZE * _EE_USE_FLASH_PAGE_OR_SECTOR))
#define   _EE_PAGE_OR_SECTOR    PAGE
#if (_EE_USE_FLASH_PAGE_OR_SECTOR > 31)
#error  "Please Enter currect address, maximum is (31)"
#endif
#endif

#if defined(STM32F030x8) || defined(STM32F042x8)
#define   _EE_SIZE              1024
#define   _EE_ADDR_INUSE        (((uint32_t)0x08000000) | (_EE_SIZE * _EE_USE_FLASH_PAGE_OR_SECTOR))
#define   _EE_PAGE_OR_SECTOR    PAGE
#if (_EE_USE_FLASH_PAGE_OR_SECTOR > 63)
#error  "Please Enter currect address, maximum is (63)"
#endif
#endif

#if defined(STM32F070xB)
#define   _EE_SIZE              2048
#define   _EE_ADDR_INUSE        (((uint32_t)0x08000000) | (_EE_SIZE * _EE_USE_FLASH_PAGE_OR_SECTOR))
#define   _EE_PAGE_OR_SECTOR    PAGE
#if (_EE_USE_FLASH_PAGE_OR_SECTOR > 63)
#error  "Please Enter currect address, maximum is (63)"
#endif
#endif

#if defined(STM32F070xC)
#define   _EE_SIZE              2048
#define   _EE_ADDR_INUSE        (((uint32_t)0x08000000) | (_EE_SIZE * _EE_USE_FLASH_PAGE_OR_SECTOR))
#define   _EE_PAGE_OR_SECTOR    PAGE
#if (_EE_USE_FLASH_PAGE_OR_SECTOR > 127)
#error  "Please Enter currect address, maximum is (127)"
#endif
#endif


#if defined(STM32F405xx) || defined(STM32F407xx) || defined(STM32F415xx) || defined(STM32F417xx)
#define   _EE_SIZE              (1024 * 128)
#define   _EE_ADDR_INUSE        (((uint32_t)0x08020000) | (_EE_SIZE*(_EE_USE_FLASH_PAGE_OR_SECTOR - 5)))
#define   _EE_FLASH_BANK        FLASH_BANK_1
#define   _EE_VOLTAGE_RANGE     _EE_VOLTAGE
#define   _EE_PAGE_OR_SECTOR    PAGE
#if (_EE_USE_FLASH_PAGE_OR_SECTOR > 11)
#error  "Please Enter currect address, maximum is (11)"
#endif
#if (_EE_USE_FLASH_PAGE_OR_SECTOR < 5)
#error  "Please Enter currect address, minimum is (5)"
#endif
#endif

//##########################################################################################################
uint8_t ee_format()
{	
  uint32_t	error;
	HAL_FLASH_Unlock();
	FLASH_EraseInitTypeDef	flashErase;
  #if _EE_PAGE_OR_SECTOR == PAGE
	flashErase.NbPages = 1;
  flashErase.PageAddress = _EE_ADDR_INUSE;
  flashErase.TypeErase = FLASH_TYPEERASE_PAGES;
  #else
  flashErase.NbSectors = 1;
  flashErase.Sector =  _EE_ADDR_INUSE;
  flashErase.TypeErase = FLASH_TYPEERASE_SECTORS;
  #endif
	#ifdef _EE_FLASH_BANK
	flashErase.Banks = _EE_FLASH_BANK;
	#endif
  #ifdef _EE_VOLTAGE_RANGE
  flashErase.VoltageRange = _EE_VOLTAGE_RANGE;
  #endif
	if (HAL_FLASHEx_Erase(&flashErase, &error) == HAL_OK)
	{
		HAL_FLASH_Lock();
		if(error != 0xFFFFFFFF)
			return 0;
    return 1;	
	}
	HAL_FLASH_Lock();
	return 0;	
}
//##########################################################################################################
uint8_t ee_read(uint32_t startVirtualAddress, uint32_t len, uint8_t* data)
{
	if ((startVirtualAddress + len) >	_EE_SIZE)
		return 0;
	for (uint32_t	i = startVirtualAddress ; i < len + startVirtualAddress ; i++)
	{
    if (data != NULL)
    {
      *data =  (*(__IO uint8_t*)(i + _EE_ADDR_INUSE));
      data++;
    }	
	}
	return 1;
}
//##########################################################################################################
uint8_t ee_write(uint32_t startVirtualAddress, uint32_t len, uint8_t* data)
{
	if ((startVirtualAddress + len) >	_EE_SIZE)
		return 0;
  if (data == NULL)
    return 0;
	HAL_FLASH_Unlock();
  #ifdef FLASH_TYPEPROGRAM_BYTE
  for (uint32_t i = 0; i < len ; i++)
	{		
		if (HAL_FLASH_Program(FLASH_TYPEPROGRAM_BYTE, ((i + startVirtualAddress)) + _EE_ADDR_INUSE, (uint64_t)(data[i])) != HAL_OK)
		{
			HAL_FLASH_Lock();
			return 0;
		}
	}	
  #else
  for (uint32_t i = 0; i < len ; i+=2)
	{		
		if (HAL_FLASH_Program(FLASH_TYPEPROGRAM_HALFWORD, ((i + startVirtualAddress)) + _EE_ADDR_INUSE, (uint64_t)(data[i] | (data[i+1] << 8))) != HAL_OK)
		{
			HAL_FLASH_Lock();
			return 0;
		}
	}	
  #endif  
	HAL_FLASH_Lock();
	return 1;
}

//##########################################################################################################
uint32_t  ee_maxVirtualAddress(void)
{
  return (_EE_SIZE);  
}
//##########################################################################################################
