dekuNukem/daytripper/firmware/code/others/stable_2019/rx/Src/keyboard.c

#include <stdio.h>
#include <string.h>
#include <stdlib.h>
#include "usb_device.h"
#include "usbd_hid.h"
#include "keyboard.h"
#include "shared.h"

#define SHIFT 0x80
const uint8_t _asciimap[128] =
{
  0x00,             // NUL
  0x00,             // SOH
  0x00,             // STX
  0x00,             // ETX
  0x00,             // EOT
  0x00,             // ENQ
  0x00,             // ACK  
  0x00,             // BEL
  0x2a,     // BS Backspace
  0x2b,     // TAB  Tab
  0x28,     // LF Enter
  0x00,             // VT 
  0x00,             // FF 
  0x00,             // CR 
  0x00,             // SO 
  0x00,             // SI 
  0x00,             // DEL
  0x00,             // DC1
  0x00,             // DC2
  0x00,             // DC3
  0x00,             // DC4
  0x00,             // NAK
  0x00,             // SYN
  0x00,             // ETB
  0x00,             // CAN
  0x00,             // EM 
  0x00,             // SUB
  0x00,             // ESC
  0x00,             // FS 
  0x00,             // GS 
  0x00,             // RS 
  0x00,             // US 

  0x2c,      //  ' '
  0x1e|SHIFT,    // !
  0x34|SHIFT,    // "
  0x20|SHIFT,    // #
  0x21|SHIFT,    // $
  0x22|SHIFT,    // %
  0x24|SHIFT,    // &
  0x34,          // '
  0x26|SHIFT,    // (
  0x27|SHIFT,    // )
  0x25|SHIFT,    // *
  0x2e|SHIFT,    // +
  0x36,          // ,
  0x2d,          // -
  0x37,          // .
  0x38,          // /
  0x27,          // 0
  0x1e,          // 1
  0x1f,          // 2
  0x20,          // 3
  0x21,          // 4
  0x22,          // 5
  0x23,          // 6
  0x24,          // 7
  0x25,          // 8
  0x26,          // 9
  0x33|SHIFT,      // :
  0x33,          // ;
  0x36|SHIFT,      // <
  0x2e,          // =
  0x37|SHIFT,      // >
  0x38|SHIFT,      // ?
  0x1f|SHIFT,      // @
  0x04|SHIFT,      // A
  0x05|SHIFT,      // B
  0x06|SHIFT,      // C
  0x07|SHIFT,      // D
  0x08|SHIFT,      // E
  0x09|SHIFT,      // F
  0x0a|SHIFT,      // G
  0x0b|SHIFT,      // H
  0x0c|SHIFT,      // I
  0x0d|SHIFT,      // J
  0x0e|SHIFT,      // K
  0x0f|SHIFT,      // L
  0x10|SHIFT,      // M
  0x11|SHIFT,      // N
  0x12|SHIFT,      // O
  0x13|SHIFT,      // P
  0x14|SHIFT,      // Q
  0x15|SHIFT,      // R
  0x16|SHIFT,      // S
  0x17|SHIFT,      // T
  0x18|SHIFT,      // U
  0x19|SHIFT,      // V
  0x1a|SHIFT,      // W
  0x1b|SHIFT,      // X
  0x1c|SHIFT,      // Y
  0x1d|SHIFT,      // Z
  0x2f,          // [
  0x31,          // bslash
  0x30,          // ]
  0x23|SHIFT,    // ^
  0x2d|SHIFT,    // _
  0x35,          // `
  0x04,          // a
  0x05,          // b
  0x06,          // c
  0x07,          // d
  0x08,          // e
  0x09,          // f
  0x0a,          // g
  0x0b,          // h
  0x0c,          // i
  0x0d,          // j
  0x0e,          // k
  0x0f,          // l
  0x10,          // m
  0x11,          // n
  0x12,          // o
  0x13,          // p
  0x14,          // q
  0x15,          // r
  0x16,          // s
  0x17,          // t
  0x18,          // u
  0x19,          // v
  0x1a,          // w
  0x1b,          // x
  0x1c,          // y
  0x1d,          // z
  0x2f|SHIFT,    // {
  0x31|SHIFT,    // |
  0x30|SHIFT,    // }
  0x35|SHIFT,    // ~
  0       // DEL
};

uint8_t kb_buf[KB_BUF_SIZE] = {1, 0, 0, 0, 0};

void print_kb_buf(void)
{
  for (int i = 0; i < KB_BUF_SIZE; ++i)
    printf("0x%x ", kb_buf[i]);
  printf("\n");
}

void keyboard_release_all(void)
{
  for (int i = 1; i < KB_BUF_SIZE; ++i)
    kb_buf[i] = 0;
  USBD_HID_SendReport(&hUsbDeviceFS, kb_buf, KB_BUF_SIZE);
}

uint8_t is_media_key(uint8_t k)
{
  return k == KEY_VOL_UP || k == KEY_VOL_DOWN || k == KEY_VOL_MUTE;
}

void media_key_press(uint8_t k)
{
  uint8_t usage_id = 0;
  if(k == KEY_VOL_UP)
    usage_id = 0x80;
  else if(k == KEY_VOL_DOWN)
    usage_id = 0x81;
  else if(k == KEY_VOL_MUTE)
    usage_id = 0x7f;

  for (int i = 1; i < KB_BUF_SIZE; ++i)
    kb_buf[i] = 0;
  kb_buf[2] = usage_id;
  USBD_HID_SendReport(&hUsbDeviceFS, kb_buf, KB_BUF_SIZE);
}

void keyboard_press(uint8_t k, uint8_t use_mod)
{
  uint8_t usage_id;

  if(is_media_key(k))
  {
    media_key_press(k);
    return;
  }

  if(k >= 0x88)
    usage_id = k - 0x88;
  else if(k >= 0x80)
  {
    kb_buf[1] |= (1<<(k-0x80));
    usage_id = 0;
  }
  else
    usage_id = _asciimap[k];

  if(use_mod && (usage_id & 0x80))
    kb_buf[1] |= 0x2;
  usage_id = usage_id & 0x7f;
  if(kb_buf[2] != usage_id && kb_buf[3] != usage_id && kb_buf[4] != usage_id)
  {
    for (int i = 2; i < KB_BUF_SIZE; ++i)
      if(kb_buf[i] == 0)
      {
        kb_buf[i] = usage_id;
        break;
      }
  }
  USBD_HID_SendReport(&hUsbDeviceFS, kb_buf, KB_BUF_SIZE);
}

void keyboard_release(uint8_t k)
{
  uint8_t usage_id;

  if(is_media_key(k))
  {
    keyboard_release_all();
    return;
  }

  if(k >= 0x88)
    usage_id = k - 0x88;
  else if(k >= 0x80)
  {
    kb_buf[1] &= ~(1<<(k-0x80));
    usage_id = 0;
  }
  else
    usage_id = _asciimap[k];

  if(usage_id & 0x80)
    kb_buf[1] &= ~(0x02);
  usage_id = usage_id & 0x7f;

  for (int i = 2; i < KB_BUF_SIZE; ++i)
    if(kb_buf[i] == usage_id)
      kb_buf[i] = 0;

  USBD_HID_SendReport(&hUsbDeviceFS, kb_buf, KB_BUF_SIZE);
}

void kb_print(char* msg, uint16_t chardelay)
{
  HAL_IWDG_Refresh(&hiwdg);
  for (int i = 0; i < strlen(msg); ++i)
  {
    keyboard_press(msg[i], 1);
    HAL_Delay(chardelay);
    HAL_IWDG_Refresh(&hiwdg);
    
    keyboard_release(msg[i]);
    HAL_Delay(chardelay);
    HAL_IWDG_Refresh(&hiwdg);
  }
}

void kb_test(void)
{
  ;
}
