dekuNukem/daytripper/firmware/code/tx/Inc/eeConfig.h

#ifndef __EECONFIG_H
#define __EECONFIG_H

#define   _EE_USE_FLASH_PAGE_OR_SECTOR              (31)
#define   _EE_VOLTAGE                               FLASH_VOLTAGE_RANGE_3 //  use in some devices
#endif
