dekuNukem/daytripper/firmware/code/tx/Src/my_usb.c

#include <stdio.h>
#include <string.h>
#include <stdlib.h>
#include "my_usb.h"
#include "usbd_cdc_if.h"

char* usb_data;
linear_buf usb_recv_buf;
volatile int32_t port_opened;
char usb_line_buf[USB_BUF_SIZE];

void my_usb_init(void)
{
  port_opened = 0;
  linear_buf_init(&usb_recv_buf, USB_BUF_SIZE);
}

void my_usb_putchar(uint8_t ch)
{
  int32_t start = HAL_GetTick();
  while(port_opened)
  {
    uint8_t result = CDC_Transmit_FS(&ch, 1);
    if(result == USBD_OK || result == USBD_FAIL)
      return;
    if(HAL_GetTick() - start > 100)
      port_opened = 0;
  }
}

char* my_usb_readline(void)
{
  char* ret = NULL;
  if(usb_recv_buf.curr_index > 0)
  {
    if(usb_recv_buf.buf[usb_recv_buf.curr_index - 1] == '\n')
    {
      for (int i = 0; i < usb_recv_buf.curr_index; ++i)
        if(usb_recv_buf.buf[i] == '\n' || usb_recv_buf.buf[i] == '\r')
          usb_recv_buf.buf[i] = 0;
      memset(usb_line_buf, 0, USB_BUF_SIZE);
      strcpy(usb_line_buf, (const char *)usb_recv_buf.buf);
      ret = usb_line_buf;
      linear_buf_reset(&usb_recv_buf);
    }
    else if(HAL_GetTick() - usb_recv_buf.last_recv > 500)
      linear_buf_reset(&usb_recv_buf);
  }
  return ret;
}
