dekuNukem/daytripper/firmware/code/others/stable_2019/rx/Src/radioPinFunctions.c

#include "nrf24.h"
#include "shared.h"

void nrf24_ce_digitalWrite(uint8_t state)
{
    if(state)
        HAL_GPIO_WritePin(NRF_CE_GPIO_Port, NRF_CE_Pin, GPIO_PIN_SET);
    else
        HAL_GPIO_WritePin(NRF_CE_GPIO_Port, NRF_CE_Pin, GPIO_PIN_RESET);
}

void nrf24_csn_digitalWrite(uint8_t state)
{
    if(state)
        HAL_GPIO_WritePin(SPI1_CS_GPIO_Port, SPI1_CS_Pin, GPIO_PIN_SET);
    else
        HAL_GPIO_WritePin(SPI1_CS_GPIO_Port, SPI1_CS_Pin, GPIO_PIN_RESET);
}
