dekuNukem/daytripper/firmware/code/others/experimental/tx_eeprom_new_sensor/Inc/eeConfig.h

#ifndef __EECONFIG_H
#define __EECONFIG_H

#define   _EE_USE_FLASH_PAGE_OR_SECTOR              (30)
#define   _EE_VOLTAGE                               FLASH_VOLTAGE_RANGE_3 //  use in some devices
#endif
