dekuNukem/daytripper/firmware/range_test/f030_rx/temp.c

uint8_t spi_transfer(uint8_t tx)
{
    uint8_t i = 0;
    uint8_t rx = 0;    
HAL_SPI_TransmitReceive
    nrf24_sck_digitalWrite(LOW);

    for(i=0;i<8;i++)
    {

        if(tx & (1<<(7-i)))
        {
            nrf24_mosi_digitalWrite(HIGH);            
        }
        else
        {
            nrf24_mosi_digitalWrite(LOW);
        }

        nrf24_sck_digitalWrite(HIGH);        

        rx = rx << 1;
        if(nrf24_miso_digitalRead())
        {
            rx |= 0x01;
        }

        nrf24_sck_digitalWrite(LOW);                

    }

    return rx;
}


    HAL_GPIO_TogglePin(SPI1_CS_GPIO_Port, SPI1_CS_Pin);
    printf("hello world\n");
    HAL_Delay(200);
